AliakseiHryhoryeu/graduate-work-construction-engineer/Приложения/Приложение А.rtf

1. Плита: Плита87 - Плита № 87

1.1. Армирование:

• Тип : Плиты
• Направление рабочей арматуры : 0°
Основной класс арматуры : Нормативная прочность = 500,00 МПа
Горизонтальная ветвь графика зависимости напряжений от деформации
• Класс пластичности : C
• Диаметры стержней нижняя d1 = 1,6 (см) d2 = 1,6 (см)
верх d1 = 1,6 (см) d2 = 1,6 (см)
• Защитный слой нижняя c1 = 3,0 (см)
верх c2 = 3,0 (см)
• Отклонения защитного слоя Cdev = 1,0(см), Cdur = 0,0(см)

1.2. Бетон

Класс : C25/30; Нормативная прочность = 25,00 МПа
Прямоугольное распределение напряжений [3.1.7(3)]
• Плотность : 2501,36 (кГ/м3)
• Коэффициент ползучести бетона : 1,53
• Марка цемента : N

1.3. Гипотеза

• Расчеты по : EN 1992-1-1:2004/A1:2014
• Методы расчета площади арматуры : аналитический
• Допустимая ширина раскрытия трещин
- верхний слой : 0,40 (мм)
- нижний слой : 0,40 (мм)
• Допустимый прогиб : 3,0 (см)
• Проверка продавливания : да
• Внешние воздействия
- верхний слой : X0
- нижний слой : X0
• Тип расчета : чистый изгиб
• Класс конструкции : S1

1.4. Геометрия пластины

Толщина 0,30 (м)

Контур:
ребро начало конец длина
x1 y1 x2 y2 (м)
1 13,60 -27,25 13,60 -7,20 20,05
2 13,60 -7,20 13,71 -7,20 0,11
3 13,71 -7,20 14,33 -7,20 0,62
4 14,33 -7,20 14,91 -6,62 0,82
5 14,91 -6,62 14,91 -0,58 6,04
6 14,91 -0,58 14,33 0,00 0,82
7 14,33 0,00 13,71 0,00 0,62
8 13,71 0,00 0,00 0,00 13,71
9 0,00 0,00 0,00 -18,00 18,00
10 0,00 -18,00 -1,80 -18,00 1,80
11 -1,80 -18,00 -1,80 -43,20 25,20
12 -1,80 -43,20 -0,00 -43,20 1,80
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
22 11,97 8
28 0,54 40
28 0,74 38
28 3,13 4
28 3,33 20
28 6,04 2
28 6,34 2
28 6,64 2
28 6,83 32
28 6,94 2
28 7,14 10
28 7,36 16
28 8,40 18
28 8,46 16
28 8,92 24
28 8,93 9
28 9,00 8
28 9,44 8
28 9,45 12
28 9,60 18
28 9,97 12
28 10,13 11
28 10,66 4
28 10,73 94
28 11,26 188
28 11,36 20
28 11,90 30
