AliakseiHryhoryeu/graduate-work-construction-engineer/2. Расчетно-конструктивный раздел/Мое/Расчетный раздел.docx

2 Расчетно – конструктивный раздел

2.1 Расчет и конструирование перекрытия кровли в монолитном

железобетоне

Дипломный проект выполнен в монолитном железобетонном исполнении и включает в себя расчет и конструирование программным методом монолитного перекрытия. Расчет выполняется с применением программ Autodesk Robot Structural Analysis Professional 2021 путем интеграции 3D модели проекта из Autodesk Revit 2021. Результаты расчета и армирования экспортируются в изначальную модель для формирования необходимых чертежей.

Таблица 2.1 – Исходные данные

Тип здания | Гражданское
Размер здания в плане А х Б | 14,2х60,0 м
Количество этажей n1 | 10
Высота этажа Н1 | 3 м
Район строительства | г.Минск
Снеговая нагрузка S0 | 1,87 кПа

Таблица 2.2 – Характеристики материалов монолитного варианта

Конструкция | Класс бетона | Класс рабочей арматуры
Плита | С25/30 | S500

2.2 Подсчет нагрузок на плиту

Таблица 2.3 Нагрузки на плиту покрытия

Вид нагрузки | Нормативная нагрузка, кПа | | Расчетная нагруз- ка, кПа
Постоянная g:
ж/б плита (t=0,3м, ρ=25кН/м³) | 7,5 | 1,35 | 10,125
0,3∙25=7,5 кПа
Пароизоляционная пленка „Технониколь” (t=0,003 м, ρ=12 кН/м3) | 0,036 | 1,35 | 0,0486
0,003∙12=0,036 кПа
Керамзит(t=0,1 м, ρ=2 кН/м3) | 0,2 | 1,35 | 0.27
0,1∙2=0,2 кПа
Теплоизоляция из пенополистирола (t=0,3м, ρ=1,25 кН/м³) | 0,125 | 1,35 | 0,167
0,25∙0,5=0,125 кПа
Цементно-песчаная стряжка М100(t=0,03 м, ρ=24 кН/м³) | 0,72 | 1,35 | 0,972
0,03∙24=0,72 кПа
Два слоя битумно-полимерного материала ”Кровляэласт” К-СТ-БЭ-М/ПП-3,5 СТБ 1107-98 (t=0,003 м, ρ=12,0 кН/м³) | 0,036 | 1,35 | 0,049
0,003∙12=0,36 кПа
Итого постоянная: | gk=8.617 | | gd=11.632
Переменная q: снег | 1,872 | 1,5 | 2,823

Расчет программным комплексом Autodesk Robot Structural Analysis 2021 представлен в приложении А.

Изм. Кол. Лист №док. Подпись Дата Лист 923/21 - ПЗ
