AliakseiHryhoryeu/graduate-work-construction-engineer/5. Экономика/Курсовой/Приложение Г.rtf

www.BelStroyka.by верс. 1.17.13 | Приложение Г
Подрядчик: Наименование подрядчика
Наименование объекта:
Код объекта:
В е д о м о с т ь о б ъ е м о в р а б о т и р а с х о д а р е с у р с о в
Обоснование | Наименование видов работ | Объем | Наименование ресурсов | Единица измерения | Количество
| | Единица измерения
1 | 2 | 3 | 4 | 5 | 6
| Подземная часть | | Трудозатраты рабочих | чел.-час. | 79.36
| | | Трудозатраты рабочих, обслуживающих машины и механизмы | чел.-час. | 106.17
| | | Механизмы
М060247 | | | Экскаваторы одноковшовые дизельные на гусеничном ходу 0,5 м3 | МАШ.-Ч | 77.9218
М070149 | | | Бульдозеры 79 (108) квт (л.с.) | МАШ.-Ч | 28.2525
| | | Материалы
С412-1290-3 | | | Щебень из гравия марки 800, 2 класса, фракции 20-80 мм | М3 | 0.0729
| Фундаменты | | Трудозатраты рабочих | чел.-час. | 20621.34
| | | Трудозатраты рабочих, обслуживающих машины и механизмы | чел.-час. | 1330.54
| | | Механизмы
М020129 | | | Краны башенные 8 т | МАШ.-Ч | 206.9064
М020130 | | | Краны башенные 10 т | МАШ.-Ч | 173.9203
М021141 | | | Краны на автомобильном ходу 10 т | МАШ.-Ч | 49.5628
М030101 | | | Автопогрузчики 5 т | МАШ.-Ч | 81.57556
М040502 | | | Установки для сварки ручной дуговой (постоянного тока) | МАШ.-Ч | 183.0918
М050102 | | | Компрессоры передвижные с двигателем внутреннего сгорания давлением до 686 кпа (7атм) 5 м3/мин | МАШ.-Ч | 64.554
М070149 | | | Бульдозеры 79 (108) квт (л.с.) | МАШ.-Ч | 2.955
М110101 | | | Бадьи емкостью 2 м3 | МАШ.-Ч | 70.525
М110102 | | | Бадьи емкостью 4 м3 | МАШ.-Ч | 77.6677
М110610 | | | Смеситель-перегружатель 3 м3 | МАШ.-Ч | 2.1762
М110907 | | | Вибраторы | МАШ.-Ч | 77.6677
М111100 | | | Вибратор глубинный | МАШ.-Ч | 46.025
М121003 | | | Котлы битумные передвижные 400 л | МАШ.-Ч | 14.8707
М140110 | | | Агрегаты копровые без дизель-молота на базе трактора 80 (108) квт (л.с.) | МАШ.-Ч | 561.792
М140504 | | | Дизель-молоты 2,5 т | МАШ.-Ч | 561.792
М150702 | | | Краны-трубоукладчики для труб диаметром до 700 мм, грузоподъемностью 12,5 т | МАШ.-Ч | 155.648
М330302 | | | Машины шлифовальные угловые | МАШ.-Ч | 3.15
М331101 | | | Трамбовки пневматические (без учета стоимости сжатого воздуха) | МАШ.-Ч | 64.554
М331617 | | | Средства малой механизации | МАШ.-Ч | 31.4523
| | | Материалы
С101-129900 | | | Топливо дизельное из малосернистых нефтей | Т | 0.218426
С101-151300 | | | Электроды типа э42 диаметром 4 мм | Т | 0.000245

Обоснование | Наименование видов работ | Объем | Наименование ресурсов | Единица измерения | Количество
| | Единица измерения
1 | 2 | 3 | 4 | 5 | 6
С101-152900 | | | Электроды типа э42 диаметром 6 мм | Т | 0.2254
С101-17500-1 | | | Гвозди строительные | КГ | 108.328
С101-47101 | | | Краска масляная ма-15, сурик железный | Т | 0.0031616
С101-48604 | | | Круг отрезной 125х1,6х22 для резки металла | ШТ | 0.7875
С101-61200 | | | Мастика битумно-масляная морозостойкая мб-50 | Т | 1.6926
С101-81600 | | | Проволока стальная низкоуглеродистая общего назначения термически обработанная, без покрытия (светлая и черная), диаметром 1,1 мм | Т | 0.07
С101-85801 | | | Рубероид подкладочный с пылевидной посыпкой рпп-300 | М2 | 886.6
С101-87400 | | | Сетка проволочная тканая с квадратными ячейками n 05 без покрытия | М2 | 9.24
С101-96200 | | | Смазка солидол жировой (солидол-ж) | Т | 0.15543
С102-16000 | | | Доски обрезные из мягколиственных пород и березы длиной 4-6,5 м, толщиной 45 мм и более, 2 сорта | М3 | 1.4592
С102-2500 | | | Бруски обрезные хвойных пород длиной 4-6,5 м, шириной 75-150 мм, толщиной 40-75 мм, 3 сорта | М3 | 5.206
С102-3200 | | | Брусья обрезные хвойных пород длиной 4-6,5 м, шириной 150мм, толщиной 150 мм и более, 2 сорта | М3 | 0.822
С102-5300 | | | Доски обрезные хвойных пород длиной 4-6,5 м, шириной 75-150 мм, толщиной 25 мм, 3 сорта | М3 | 0.4384
С102-6100 | | | Доски обрезные хвойных пород длиной 4-6,5 м, шириной 75-150 мм, толщиной 44 мм и более, 3 сорта | М3 | 2.3288
С102-8000 | | | Доски необрезные хвойных пород длиной 4-6,5 м, толщиной 44 мм и более, 2 сорта | М3 | 0.2478
С113-12904-12 | | | Пленка полиэтиленовая первого сорта, толщиной 0,2 мм | М2 | 180.0575
С203-49801 | | | Щиты из досок толщина 25 мм | М2 | 92.082
С203-49802 | | | Щиты из досок толщина 40 мм | М2 | 12.312
С204-2900 | | | Заготовки из проволоки из низкоуглеродистой стали холоднотянутой периодического профиля класса вр-i для армирования железобетонных конструкций диаметром 4 мм | Т | 11.086912
С204-6200 | | | Детали закладные, изготовленные без применения сварки, гнутья, сверления (пробивки) отверстий, поставляемые отдельно | Т | 0.07
С204-6400 | | | Детали закладные, изготовленные с применением сварки, гнутья, сверления (пробивки) отверстий (при наличии одной из этих операций или всего перечня в любых сочетаниях), поставляемые отдельно | Т | 2.432
С412-9005 | | | Вода | М3 | 2.394
С414-1003 | | | Бетон тяжелый с крупностью заполнителя 20-40 мм, класса в7,5 | М3 | 347.13
С414-1005 | | | Бетон тяжелый с крупностью заполнителя 20-40 мм, класса с12/15 (b15) | М3 | 14.21
С414-1005-3 | | | Бетон тяжелый с крупностью заполнителя более 10 до 20 мм, класса с12/15 (b15) | М3 | 139.055
С414-1009 | | | Бетон тяжелый с крупностью заполнителя 20-40 мм, класса с25/30 (в30) | М3 | 177.625
С414-2001 | | | Растворы кладочные тяжелые цементные, марки 25 | М3 | 10.075
С101-115100 | | | Сталь арматурная горячекатаная гладкая для железобетонных конструкций, класса s240 (а240), диаметром 12 мм | Т | 431.055
С101-118715 | | | Сталь арматурная горячекатаная периодического профиля для железобетонных конструкций, класса s500, диаметром 20 мм | Т | 143.685
| Несущие конструкции | | Трудозатраты рабочих | чел.-час. | 67520.41
| | | Трудозатраты рабочих, обслуживающих машины и механизмы | чел.-час. | 1486.24
| | | Механизмы
М020129 | | | Краны башенные 8 т | МАШ.-Ч | 661.5864
М020130 | | | Краны башенные 10 т | МАШ.-Ч | 331.356
М021141 | | | Краны на автомобильном ходу 10 т | МАШ.-Ч | 53.0276
М030101 | | | Автопогрузчики 5 т | МАШ.-Ч | 268.2288

Обоснование | Наименование видов работ | Объем | Наименование ресурсов | Единица измерения | Количество
| | Единица измерения
1 | 2 | 3 | 4 | 5 | 6
М040502 | | | Установки для сварки ручной дуговой (постоянного тока) | МАШ.-Ч | 1894.9606
М110101 | | | Бадьи емкостью 2 м3 | МАШ.-Ч | 47.304
М110102 | | | Бадьи емкостью 4 м3 | МАШ.-Ч | 601.509
М110907 | | | Вибраторы | МАШ.-Ч | 601.509
М111100 | | | Вибратор глубинный | МАШ.-Ч | 41.2308
М330302 | | | Машины шлифовальные угловые | МАШ.-Ч | 0.7848
М331617 | | | Средства малой механизации | МАШ.-Ч | 172.0374
| | | Материалы
С101-151300 | | | Электроды типа э42 диаметром 4 мм | Т | 0.0003204
С101-152900 | | | Электроды типа э42 диаметром 6 мм | Т | 2.3308
С101-17500-1 | | | Гвозди строительные | КГ | 1095.324
С101-48604 | | | Круг отрезной 125х1,6х22 для резки металла | ШТ | 0.198
С101-81600 | | | Проволока стальная низкоуглеродистая общего назначения термически обработанная, без покрытия (светлая и черная), диаметром 1,1 мм | Т | 0.0195192
С101-96200 | | | Смазка солидол жировой (солидол-ж) | Т | 1.4521
С102-2500 | | | Бруски обрезные хвойных пород длиной 4-6,5 м, шириной 75-150 мм, толщиной 40-75 мм, 3 сорта | М3 | 52.06
С102-3200 | | | Брусья обрезные хвойных пород длиной 4-6,5 м, шириной 150мм, толщиной 150 мм и более, 2 сорта | М3 | 8.22
С102-5300 | | | Доски обрезные хвойных пород длиной 4-6,5 м, шириной 75-150 мм, толщиной 25 мм, 3 сорта | М3 | 4.384
С102-6100 | | | Доски обрезные хвойных пород длиной 4-6,5 м, шириной 75-150 мм, толщиной 44 мм и более, 3 сорта | М3 | 21.92
С102-8000 | | | Доски необрезные хвойных пород длиной 4-6,5 м, толщиной 44 мм и более, 2 сорта | М3 | 3.0444
С113-12904-12 | | | Пленка полиэтиленовая первого сорта, толщиной 0,2 мм | М2 | 329.452
С203-49801 | | | Щиты из досок толщина 25 мм | М2 | 966.58
С204-2900 | | | Заготовки из проволоки из низкоуглеродистой стали холоднотянутой периодического профиля класса вр-i для армирования железобетонных конструкций диаметром 4 мм | Т | 35.806708
С204-6200 | | | Детали закладные, изготовленные без применения сварки, гнутья, сверления (пробивки) отверстий, поставляемые отдельно | Т | 0.0915624
С414-1005 | | | Бетон тяжелый с крупностью заполнителя 20-40 мм, класса с12/15 (b15) | М3 | 174.58
С414-1005-3 | | | Бетон тяжелый с крупностью заполнителя более 10 до 20 мм, класса с12/15 (b15) | М3 | 1390.55
С414-1009 | | | Бетон тяжелый с крупностью заполнителя 20-40 мм, класса с25/30 (в30) | М3 | 36.54
С101-115100 | | | Сталь арматурная горячекатаная гладкая для железобетонных конструкций, класса s240 (а240), диаметром 12 мм | Т | 1378.306
С101-118715 | | | Сталь арматурная горячекатаная периодического профиля для железобетонных конструкций, класса s500, диаметром 20 мм | Т | 459.435
| Наружная отделка фасадов | | Трудозатраты рабочих | чел.-час. | 17953.75
| | | Трудозатраты рабочих, обслуживающих машины и механизмы | чел.-час. | 1437.94
| | | Механизмы
М020130 | | | Краны башенные 10 т | МАШ.-Ч | 159.7008
М021141 | | | Краны на автомобильном ходу 10 т | МАШ.-Ч | 11.8768
М050102 | | | Компрессоры передвижные с двигателем внутреннего сгорания давлением до 686 кпа (7атм) 5 м3/мин | МАШ.-Ч | 898.3854
М330302 | | | Машины шлифовальные угловые | МАШ.-Ч | 91.8136
М331400 | | | Станок камнерезный универсальный | МАШ.-Ч | 88.8777
М331451 | | | Перфораторы электрические | МАШ.-Ч | 561.0238

Обоснование | Наименование видов работ | Объем | Наименование ресурсов | Единица измерения | Количество
| | Единица измерения
1 | 2 | 3 | 4 | 5 | 6
М331604 | | | Станок передвижной для сверления отверстий в железобетоне диаметром 20-160 мм | МАШ.-Ч | 890.3784
М331615 | | | Дрели электрические | МАШ.-Ч | 1148.4175
М331617 | | | Средства малой механизации | МАШ.-Ч | 279.1048
М351302 | | | Электрофен | МАШ.-Ч | 222.5946
| | | Материалы
С101-10110-1 | | | Болты строительные с гайками и шайбами диаметром 8-12мм | Т | 0.341632
С101-115000 | | | Сталь арматурная горячекатаная гладкая для железобетонных конструкций, класса s240 (а240), диаметром 10 мм | Т | 0.99813
С101-11602-15 | | | Винты самонарезающие с полукруглой головкой диаметром 6-10мм длиной 50мм | КГ | 62.3532
С101-11602-6 | | | Винты с полукруглой головкой 4х30 мм гост 17473-80 | КГ | 6.4056
С101-11602-7 | | | Винты с полукруглой головкой 5х20 мм гост 17473-80 | КГ | 21.0851
С101-11602-9 | | | Винты самонарезающие с полуцилиндрической головкой для металла | КГ | 46.1737
С101-123402 | | | Сталь тонколистовая оцинкованная углеродистая толщиной 0,8 мм | КГ | 3003.2976
С101-123403 | | | Сталь тонколистовая оцинкованная углеродистая толщиной 0,5 мм | Т | 0.4810104
С101-138010 | | | Растворная смесь сухая, кладочная, цементная, для кирпича, камней, блоков, с водоудерживающей добавкой, м100/м150, f75 | Т | 20.262039
С101-149003-1 | | | Шайба плоская оцинкованная | ШТ | 13184.86
С101-149004 | | | Прокладки паронитовые | КГ | 111.0304
С101-18001 | | | Гвозди строительные оцинкованные | Т | 2.794764
С101-24301 | | | Заклепки комбинированные для соединения профилированного стального настила и разнообразных листов | Т | 0.0568497
С101-48602 | | | Круг отрезной 230х2х22 для резки камня, бетона | ШТ | 66.725
С101-48604 | | | Круг отрезной 125х1,6х22 для резки металла | ШТ | 66.4581
С101-79201-3 | | | Прокладки изолирующие пластмассовые | ШТ | 8327.28
С101-81100 | | | Проволока стальная низкоуглеродистая общего назначения термически обработанная, оцинкованная, диаметром 1,1 мм | Т | 0.2612896
С101-81201-1 | | | Проволока стальная низкоуглеродистая общего назначения термически обработанная, оцинкованная, диаметром 5 мм | Т | 0.3236428
С101-81404-1 | | | Проволока стальная низкоуглеродистая общего назначения термически обработанная, оцинкованная, диаметром 2 мм | КГ | 41.5688
С101-82905 | | | Пряжка бандажная тип 1-о | КГ | 8.9076
С101-85801 | | | Рубероид подкладочный с пылевидной посыпкой рпп-300 | М2 | 598.878
С101-86720 | | | Сверла спиральные с цилиндрическим хвостовиком, длинная серия (по металлу), диаметром 3,1-3,7мм | ШТ | 142.7915
С101-86721 | | | Сверла спиральные с цилиндрическим хвостовиком, длинная серия (по металлу), диаметром 4,3-5,3мм | ШТ | 150.5316
С101-86723 | | | Сверла спиральные с цилиндрическим хвостовиком, длинная серия (по металлу), диаметром 9,6-10,6 мм | ШТ | 29.6259
С101-86726-38 | | | Сверла по бетону с sds хвостовиком (наконечник из твердосплавной стали), диаметром 10-12 мм, длиной 110-165 мм | ШТ | 111.0304
С104-427 | | | Плиты теплоизоляционные из минерального стекловолокна isover kl 37, толщиной 50 мм | М3 | 9.1332592
С104-713 | | | Плиты теплоизоляционные пенополистирольные ппт-15а (ппт-15н-а) | М3 | 203.61852
С204-6400 | | | Детали закладные, изготовленные с применением сварки, гнутья, сверления (пробивки) отверстий (при наличии одной из этих операций или всего перечня в любых сочетаниях), поставляемые отдельно | Т | 0.0576504
С412-9005 | | | Вода | М3 | 6.103623

Обоснование | Наименование видов работ | Объем | Наименование ресурсов | Единица измерения | Количество
| | Единица измерения
1 | 2 | 3 | 4 | 5 | 6
С414-3036-36 | | | Блоки из ячеистых бетонов стеновые мелкие, 1 категории, класс бетона в2, плотность 600 кг/м3 | М3 | 818.4666
| Стены и перегородки | | Трудозатраты рабочих | чел.-час. | 5559.43
| | | Трудозатраты рабочих, обслуживающих машины и механизмы | чел.-час. | 311.41
| | | Механизмы
М020130 | | | Краны башенные 10 т | МАШ.-Ч | 275.9932
М030101 | | | Автопогрузчики 5 т | МАШ.-Ч | 1.0875
М040502 | | | Установки для сварки ручной дуговой (постоянного тока) | МАШ.-Ч | 148.8909
М110101 | | | Бадьи емкостью 2 м3 | МАШ.-Ч | 115.9776
М110102 | | | Бадьи емкостью 4 м3 | МАШ.-Ч | 58.455
М110610 | | | Смеситель-перегружатель 3 м3 | МАШ.-Ч | 12.3332
М110907 | | | Вибраторы | МАШ.-Ч | 58.455
М111100 | | | Вибратор глубинный | МАШ.-Ч | 103.7304
М330302 | | | Машины шлифовальные угловые | МАШ.-Ч | 0.3744
М331617 | | | Средства малой механизации | МАШ.-Ч | 21.9959
| | | Материалы
С101-151300 | | | Электроды типа э42 диаметром 4 мм | Т | 0.002448
С101-152900 | | | Электроды типа э42 диаметром 6 мм | Т | 0.1725
С101-17500-1 | | | Гвозди строительные | КГ | 47.625
С101-48604 | | | Круг отрезной 125х1,6х22 для резки металла | ШТ | 0.0936
С101-81600 | | | Проволока стальная низкоуглеродистая общего назначения термически обработанная, без покрытия (светлая и черная), диаметром 1,1 мм | Т | 0.0113184
С101-96200 | | | Смазка солидол жировой (солидол-ж) | Т | 0.20625
С102-2500 | | | Бруски обрезные хвойных пород длиной 4-6,5 м, шириной 75-150 мм, толщиной 40-75 мм, 3 сорта | М3 | 6.45
С102-3200 | | | Брусья обрезные хвойных пород длиной 4-6,5 м, шириной 150мм, толщиной 150 мм и более, 2 сорта | М3 | 1.05
С102-6100 | | | Доски обрезные хвойных пород длиной 4-6,5 м, шириной 75-150 мм, толщиной 44 мм и более, 3 сорта | М3 | 1.8825
С113-12904-12 | | | Пленка полиэтиленовая первого сорта, толщиной 0,2 мм | М2 | 11.3184
С203-39600-1 | | | Пробки деревянные | М3 | 2.295657
С203-49801 | | | Щиты из досок толщина 25 мм | М2 | 137.25
С204-6200 | | | Детали закладные, изготовленные без применения сварки, гнутья, сверления (пробивки) отверстий, поставляемые отдельно | Т | 0.2614608
С412-9005 | | | Вода | М3 | 162.574
С413-2040-2 | | | Кирпич силикатный утолщенный, полнотелый, обыкновенный, рядовой размером 250х120х88 мм, марки 125 | 1000 ШТ | 107.9155
С414-1005-3 | | | Бетон тяжелый с крупностью заполнителя более 10 до 20 мм, класса с12/15 (b15) | М3 | 76.125
С414-1009 | | | Бетон тяжелый с крупностью заполнителя 20-40 мм, класса с25/30 (в30) | М3 | 73.08
С414-2008 | | | Растворы кладочные цементно-известковые, марки 50 | М3 | 58.0221
| Кровля | | Трудозатраты рабочих | чел.-час. | 2094.71
| | | Трудозатраты рабочих, обслуживающих машины и механизмы | чел.-час. | 71.73
| | | Механизмы
М020130 | | | Краны башенные 10 т | МАШ.-Ч | 8.8865
М021141 | | | Краны на автомобильном ходу 10 т | МАШ.-Ч | 0.0304
М031110 | | | Подъемники строительные 0,5 т | МАШ.-Ч | 16.416
М031801 | | | Вышки телескопические 0,35 т | МАШ.-Ч | 19.2375
М040502 | | | Установки для сварки ручной дуговой (постоянного тока) | МАШ.-Ч | 7.16

Обоснование | Наименование видов работ | Объем | Наименование ресурсов | Единица измерения | Количество
| | Единица измерения
1 | 2 | 3 | 4 | 5 | 6
М050401 | | | Компрессоры передвижные с электродвигателем давлением 600 кпа (6 атм) 0,5 м3/мин | МАШ.-Ч | 2.394
М111301 | | | Вибратор поверхностный | МАШ.-Ч | 102.6
М121003 | | | Котлы битумные передвижные 400 л | МАШ.-Ч | 33.6015
М134041 | | | Шуруповерт | МАШ.-Ч | 34.96
М150402 | | | Газовая горелка | МАШ.-Ч | 30.79
М331451 | | | Перфораторы электрические | МАШ.-Ч | 6.3308
М331615 | | | Дрели электрические | МАШ.-Ч | 89.68
М331617 | | | Средства малой механизации | МАШ.-Ч | 27.1579
| | | Материалы
С101-123403 | | | Сталь тонколистовая оцинкованная углеродистая толщиной 0,5 мм | Т | 4.959
С101-129900 | | | Топливо дизельное из малосернистых нефтей | Т | 0.48735
С101-135500 | | | Цемент гипсоглиноземистый расширяющийся | Т | 0.00064
С101-149001 | | | Шурупы-саморезы 4,8х28 мм | ШТ | 608
С101-149002 | | | Шурупы-саморезы 4,8х19 мм | ШТ | 304
С101-151400-1 | | | Электроды типа э42а диаметром 4 мм | КГ | 0.76
С101-15500-10 | | | Дюбель металлический рамный 10х72 | 10 ШТ | 15.2
С101-15512 | | | Дюбель с шурупом для быстрого монтажа 8х80 мм | 100 ШТ | 41.04
С101-19000 | | | Гвозди тарные круглые 3х80 мм | Т | 0.09747
С101-32200 | | | Керосин технический экологически чистый | Т | 1.0089
С101-59400 | | | Мастика битумная кровельная горячая | Т | 3.8304
С101-63205-1 | | | Льняная прядь | КГ | 0.24
С101-7600 | | | Битумы нефтяные кровельные марки бнк-90/30 | Т | 0.21375
С101-7800 | | | Битумы нефтяные кровельные марки бнк-45/180 | Т | 0.21375
С101-82511 | | | Смесь пропана и бутана технических | КГ | 364.9964
С101-85801 | | | Рубероид подкладочный с пылевидной посыпкой рпп-300 | М2 | 171.855
С101-86721 | | | Сверла спиральные с цилиндрическим хвостовиком, длинная серия (по металлу), диаметром 4,3-5,3мм | ШТ | 5.928
С101-86726-20 | | | Сверла по бетону с sds хвостовиком (наконечник из твердосплавной стали), диаметром 8-10 мм, длиной 260 (265) мм | ШТ | 25.65
С101-86726-38 | | | Сверла по бетону с sds хвостовиком (наконечник из твердосплавной стали), диаметром 10-12 мм, длиной 110-165 мм | ШТ | 1.52
С102-12100 | | | Доски обрезные хвойных пород длиной 2-3,75 м, шириной 75-150 мм, толщиной 44 мм и более, 3 сорта | М3 | 38.0475
С113-12904-12 | | | Пленка полиэтиленовая первого сорта, толщиной 0,2 мм | М2 | 171
С117-1404 | | | Мастика битумная полимерная холодная (мбпх) для нанесения на рулонные материалы | Т | 0.49932
С204-6400-2 | | | Крючья металлические массой 0,5 кг | КГ | 56.43
С412-9005 | | | Вода | М3 | 10.26
С414-2004 | | | Растворы кладочные тяжелые цементные, марки 100 | М3 | 27.3201
| Окна | | Трудозатраты рабочих | чел.-час. | 2113.03
| | | Трудозатраты рабочих, обслуживающих машины и механизмы | чел.-час. | 0
| | | Механизмы
М331615 | | | Дрели электрические | МАШ.-Ч | 302.2368
| | | Материалы
С101-148000 | | | Шурупы с полукруглой головкой 3,5х35 мм | Т | 0.0093819
С101-148200 | | | Шурупы с полукруглой головкой 5х70 мм | Т | 0.0741131
С101-149010-5 | | | Шурупы универсальные 6х100 мм | 1000 ШТ | 0.225

Обоснование | Наименование видов работ | Объем | Наименование ресурсов | Единица измерения | Количество
| | Единица измерения
1 | 2 | 3 | 4 | 5 | 6
С101-15500-12 | | | Дюбель полипропиленовый 10х50, 10х80 | ШТ | 7975.8
С101-21603 | | | Герметик силиконовый 280мл | ШТ | 45.88
С101-51512-7 | | | Лента паропроницаемая саморасширяющаяся уплотнительная (псул) шириной 12 мм с максимальным расширением ленты 30 мм | М | 244.65
С101-51521-2 | | | Лента самоклеящаяся неотверждаемая гидро-пароизоляционная бутилкаучуковая, армированная нетканым полотном ("викар с" марки лт (о)) шириной 120-150 мм, толщиной 1,5 мм | М | 244.65
С101-79100-1 | | | Пена полиуретановая монтажная производственная в аэрозольной упаковке | МЛ | 26382.9
С414-2004 | | | Растворы кладочные тяжелые цементные, марки 100 | М3 | 0.33
С203-52120 | | | Окно из поливинилхлоридного профиля brugmann оп а 600-600 п/о сп2 т, с поворотно-откидным устройством, с двухкамерным стеклопакетом, теплозащитное | М2 | 9.65
С203-52139 | | | Окно из поливинилхлоридного профиля brugmann оп а 1500-1500 п/о и г сп2 т, с поворотно-откидным устройством, с импостом, с глухой створкой, с двухкамерным стеклопакетом, теплозащитное | М2 | 194.48
С203-52144 | | | Окно из поливинилхлоридного профиля brugmann оп а 1500-2100 п/у и г и п/о сп2 т, с поворотным устройством, с глухой створкой, с поворотно-откидным устройством, с двумя импостами, с двухкамерным стеклопакетом, теплозащитное | М2 | 496.08
| Двери | | Трудозатраты рабочих | чел.-час. | 200.62
| | | Трудозатраты рабочих, обслуживающих машины и механизмы | чел.-час. | 10.87
| | | Механизмы
М021143 | | | Краны на автомобильном ходу 16 т | МАШ.-Ч | 0.5964
М121003 | | | Котлы битумные передвижные 400 л | МАШ.-Ч | 0.1684
М331617 | | | Средства малой механизации | МАШ.-Ч | 10.267
| | | Материалы
С101-148000 | | | Шурупы с полукруглой головкой 3,5х35 мм | Т | 4E-5
С101-17500-1 | | | Гвозди строительные | КГ | 17.047
С101-21903 | | | Вяжущее гипсовое марки г-4 нормальнотвердеющее (б), среднего помола (ii) (фасованное) | Т | 0.00146
С101-85801 | | | Рубероид подкладочный с пылевидной посыпкой рпп-300 | М2 | 8.18
С102-24600 | | | Дрова разделанные длиной 1 м осина, ольха, нижний лесосклад | М3 | 0.00684
С102-5300 | | | Доски обрезные хвойных пород длиной 4-6,5 м, шириной 75-150 мм, толщиной 25 мм, 3 сорта | М3 | 0.1376
С414-2012 | | | Растворы отделочные тяжелые известковые, в соотношении 1 3 | М3 | 0.00964
С203-20063 | | | Блок дверной наружный деревянный двупольный, частично остекленный, с порогом, щитовой дн д ч 21-12 п щ | М2 | 6
С203-19859-2 | | | Блок дверной внутренний межкомнатный деревянный, двупольный, глухой, щитовой дв1 д г 21-12 щ | М2 | 166.2
| Внутренние отделочные работы | | Трудозатраты рабочих | чел.-час. | 19176.39
| | | Трудозатраты рабочих, обслуживающих машины и механизмы | чел.-час. | 15.28
| | | Механизмы
М030401 | | | Лебедки электрические тяговым усилием до 5,79 (0,59) кн (т) | МАШ.-Ч | 13.608
М030404 | | | Лебедки электрические тяговым усилием до 31,39 (3,2) кн (т) | МАШ.-Ч | 0.49004
М331615 | | | Дрели электрические | МАШ.-Ч | 67.8081
М331617 | | | Средства малой механизации | МАШ.-Ч | 15.2753
| | | Материалы
С101-11099 | | | Шкурка шлифовальная на бумажной основе водостойкая | М2 | 315.794
С101-11401 | | | Ветошь | КГ | 14.7001
С101-138005-2 | | | Шпатлевка клеемасляная | Т | 4.77789

Обоснование | Наименование видов работ | Объем | Наименование ресурсов | Единица измерения | Количество
| | Единица измерения
1 | 2 | 3 | 4 | 5 | 6
С101-21903 | | | Вяжущее гипсовое марки г-4 нормальнотвердеющее (б), среднего помола (ii) (фасованное) | Т | 0.09
С101-32905 | | | Клей кмц (для обоев) | Т | 0.1813148
С101-34066 | | | Краска акриловая для внутренних работ (сп "колор" ооо), белая | КГ | 3112.55
С101-62617 | | | Обои бумажные дуплекс с полутоновым рисунком | 100 М2 | 140.8865
С101-63100 | | | Опилки древесные | М3 | 2.50635
С113-3601 | | | Дисперсия поливинилацетатная непластифицированная марки д50н | КГ | 350.3786
С412-9005 | | | Вода | М3 | 18.69406
С414-2013 | | | Растворы отделочные тяжелые известковые, в соотношении 1 2,5 | М3 | 0.234
С414-9014 | | | Растворы отделочные тяжелые цементные, приготовленные в построечных условиях, состав 1 3 | М3 | 40.425
С414-9015 | | | Растворы отделочные тяжелые цементно-известковые, приготовленные в построечных условиях, состав 1 1 6 | М3 | 11.202
| Тип 1(пол подвала) | | Трудозатраты рабочих | чел.-час. | 58.94
| | | Трудозатраты рабочих, обслуживающих машины и механизмы | чел.-час. | 2.75
| | | Механизмы
М050101 | | | Компрессоры передвижные с двигателем внутреннего сгорания давлением до 686 кпа (7атм) 2,2 м3/мин | МАШ.-Ч | 1.131
М110907 | | | Вибраторы | МАШ.-Ч | 7.1775
М331617 | | | Средства малой механизации | МАШ.-Ч | 1.624
| | | Материалы
С101-128902 | | | Ткань мешочная | 10 М2 | 0.58
С412-9005 | | | Вода | М3 | 5.075
С414-1004-1 | | | Бетон тяжелый с крупностью заполнителя 10 мм и менее, класса с10/12,5 (в12,5) | М3 | 2.958
| Тип 2(пол 1го этажа коридоры) | | Трудозатраты рабочих | чел.-час. | 305.07
| | | Трудозатраты рабочих, обслуживающих машины и механизмы | чел.-час. | 18.48
| | | Механизмы
М020130 | | | Краны башенные 10 т | МАШ.-Ч | 5.9598
М050101 | | | Компрессоры передвижные с двигателем внутреннего сгорания давлением до 686 кпа (7атм) 2,2 м3/мин | МАШ.-Ч | 2.0124
М110907 | | | Вибраторы | МАШ.-Ч | 12.771
М331607 | | | Машина паркетно-шлифовальная | МАШ.-Ч | 20.0466
М331617 | | | Средства малой механизации | МАШ.-Ч | 10.5126
| | | Материалы
С101-11099 | | | Шкурка шлифовальная на бумажной основе водостойкая | М2 | 51.6
С101-128902 | | | Ткань мешочная | 10 М2 | 1.032
С101-18000 | | | Гвозди строительные с плоской головкой 1,8х50 мм | Т | 0.035604
С101-18100 | | | Гвозди строительные оцинкованные 1,8х60 мм | Т | 4.5E-5
С101-65200 | | | Плиты древесноволокнистые мокрого способа производства мягкие марки м-2 толщиной 12 мм | 1000 М2 | 0.26574
С412-9005 | | | Вода | М3 | 9.03
С414-1004-1 | | | Бетон тяжелый с крупностью заполнителя 10 мм и менее, класса с10/12,5 (в12,5) | М3 | 5.2632
| Тип 3(пол 1го этажа, сан. помещения) | | Трудозатраты рабочих | чел.-час. | 115.86
| | | Трудозатраты рабочих, обслуживающих машины и механизмы | чел.-час. | 3.01
| | | Механизмы
М020130 | | | Краны башенные 10 т | МАШ.-Ч | 0.88836
М050101 | | | Компрессоры передвижные с двигателем внутреннего сгорания давлением до 686 кпа (7атм) 2,2 м3/мин | МАШ.-Ч | 0.55224

Обоснование | Наименование видов работ | Объем | Наименование ресурсов | Единица измерения | Количество
| | Единица измерения
1 | 2 | 3 | 4 | 5 | 6
М110907 | | | Вибраторы | МАШ.-Ч | 5.27106
М331617 | | | Средства малой механизации | МАШ.-Ч | 1.57884
М121003 | | | Котлы битумные передвижные 400 л | МАШ.-Ч | 1.63194
М331305 | | | Пылесос промышленный | МАШ.-Ч | 1.0089
М331615 | | | Дрели электрические | МАШ.-Ч | 0.58356
М331618 | | | Электротермос | МАШ.-Ч | 0.64782
| | | Материалы
С101-128902 | | | Ткань мешочная | 10 М2 | 0.2832
С412-9005 | | | Вода | М3 | 2.478
С414-1004-1 | | | Бетон тяжелый с крупностью заполнителя 10 мм и менее, класса с10/12,5 (в12,5) | М3 | 0.72216
С101-1002 | | | Асбест хризотиловый марки а-6к-30 | Т | 0.002832
С101-11401 | | | Ветошь | КГ | 0.378
С101-28701 | | | Плитки керамические для полов основные неглазурованные (керамогранит) размером 300х300 мм, 303х303 мм | М2 | 36.462
С101-7000 | | | Бензин автомобильный аи-95 | Т | 0.020178
С101-7300 | | | Битумы нефтяные строительные марки бн-90/10 | Т | 0.055578
С101-7400 | | | Битумы нефтяные строительные марки бн-70/30 | Т | 0.006726
С113-10100 | | | Мука андезитовая кислотоупорная марки а | Т | 0.04425
С414-1013-1 | | | Бетон легкий (аглопорито- и керамзитобетон) с крупностью заполнителя 10 мм и менее, класса в12,5 | М3 | 0.72216
| Тип 4(пол 1го этажа в комнатах) | | Трудозатраты рабочих | чел.-час. | 1089.62
| | | Трудозатраты рабочих, обслуживающих машины и механизмы | чел.-час. | 51.96
| | | Механизмы
М020130 | | | Краны башенные 10 т | МАШ.-Ч | 20.6976
М050101 | | | Компрессоры передвижные с двигателем внутреннего сгорания давлением до 686 кпа (7атм) 2,2 м3/мин | МАШ.-Ч | 6.9888
М110907 | | | Вибраторы | МАШ.-Ч | 44.352
М331617 | | | Средства малой механизации | МАШ.-Ч | 24.2816
| | | Материалы
С101-128902 | | | Ткань мешочная | 10 М2 | 3.584
С412-9005 | | | Вода | М3 | 31.36
С414-1004-1 | | | Бетон тяжелый с крупностью заполнителя 10 мм и менее, класса с10/12,5 (в12,5) | М3 | 18.2784
С101-32903 | | | Клей бустилат | Т | 0.448
С101-55700 | | | Линолеум поливинилхлоридный на тканевой подоснове, звукоизолирующий декоративный "деколин" | М2 | 946.176
| Тип 5(пол типового этажа коридоры) | | Трудозатраты рабочих | чел.-час. | 1742.56
| | | Трудозатраты рабочих, обслуживающих машины и механизмы | чел.-час. | 81.91
| | | Механизмы
М050101 | | | Компрессоры передвижные с двигателем внутреннего сгорания давлением до 686 кпа (7атм) 2,2 м3/мин | МАШ.-Ч | 16.1148
М110907 | | | Вибраторы | МАШ.-Ч | 102.267
М331607 | | | Машина паркетно-шлифовальная | МАШ.-Ч | 160.5282
М331617 | | | Средства малой механизации | МАШ.-Ч | 65.7948
| | | Материалы
С101-11099 | | | Шкурка шлифовальная на бумажной основе водостойкая | М2 | 413.2
С101-128902 | | | Ткань мешочная | 10 М2 | 8.264
С101-18000 | | | Гвозди строительные с плоской головкой 1,8х50 мм | Т | 0.285108
С101-18100 | | | Гвозди строительные оцинкованные 1,8х60 мм | Т | 0.00036

Обоснование | Наименование видов работ | Объем | Наименование ресурсов | Единица измерения | Количество
| | Единица измерения
1 | 2 | 3 | 4 | 5 | 6
С101-65200 | | | Плиты древесноволокнистые мокрого способа производства мягкие марки м-2 толщиной 12 мм | 1000 М2 | 2.12798
С412-9005 | | | Вода | М3 | 72.31
С414-1004-1 | | | Бетон тяжелый с крупностью заполнителя 10 мм и менее, класса с10/12,5 (в12,5) | М3 | 42.1464
| Тип 6(пол типового этажа, сан помещения) | | Трудозатраты рабочих | чел.-час. | 1539.68
| | | Трудозатраты рабочих, обслуживающих машины и механизмы | чел.-час. | 26.49
| | | Механизмы
М050101 | | | Компрессоры передвижные с двигателем внутреннего сгорания давлением до 686 кпа (7атм) 2,2 м3/мин | МАШ.-Ч | 7.7376
М110907 | | | Вибраторы | МАШ.-Ч | 73.8544
М331617 | | | Средства малой механизации | МАШ.-Ч | 17.7072
М020130 | | | Краны башенные 10 т | МАШ.-Ч | 1.0544
М121003 | | | Котлы битумные передвижные 400 л | МАШ.-Ч | 22.8656
М331305 | | | Пылесос промышленный | МАШ.-Ч | 14.136
М331615 | | | Дрели электрические | МАШ.-Ч | 8.9184
М331618 | | | Электротермос | МАШ.-Ч | 9.0768
| | | Материалы
С101-128902 | | | Ткань мешочная | 10 М2 | 3.968
С412-9005 | | | Вода | М3 | 34.72
С414-1004-1 | | | Бетон тяжелый с крупностью заполнителя 10 мм и менее, класса с10/12,5 (в12,5) | М3 | 10.1184
С101-1002 | | | Асбест хризотиловый марки а-6к-30 | Т | 0.03968
С101-11401 | | | Ветошь | КГ | 5.76
С101-28701 | | | Плитки керамические для полов основные неглазурованные (керамогранит) размером 300х300 мм, 303х303 мм | М2 | 510.88
С101-7000 | | | Бензин автомобильный аи-95 | Т | 0.28272
С101-7300 | | | Битумы нефтяные строительные марки бн-90/10 | Т | 0.77872
С101-7400 | | | Битумы нефтяные строительные марки бн-70/30 | Т | 0.09424
С113-10100 | | | Мука андезитовая кислотоупорная марки а | Т | 0.62
С414-1013-1 | | | Бетон легкий (аглопорито- и керамзитобетон) с крупностью заполнителя 10 мм и менее, класса в12,5 | М3 | 10.1184
| Тип 7(пол типового этажа в помещениях) | | Трудозатраты рабочих | чел.-час. | 6287.05
| | | Трудозатраты рабочих, обслуживающих машины и механизмы | чел.-час. | 186.37
| | | Механизмы
М050101 | | | Компрессоры передвижные с двигателем внутреннего сгорания давлением до 686 кпа (7атм) 2,2 м3/мин | МАШ.-Ч | 55.9104
М110907 | | | Вибраторы | МАШ.-Ч | 354.816
М331617 | | | Средства малой механизации | МАШ.-Ч | 130.4576
| | | Материалы
С101-128902 | | | Ткань мешочная | 10 М2 | 28.672
С412-9005 | | | Вода | М3 | 250.88
С414-1004-1 | | | Бетон тяжелый с крупностью заполнителя 10 мм и менее, класса с10/12,5 (в12,5) | М3 | 146.2272
С101-32903 | | | Клей бустилат | Т | 3.584
С101-55700 | | | Линолеум поливинилхлоридный на тканевой подоснове, звукоизолирующий декоративный "деколин" | М2 | 7569.408
| Отмостка и крыльца | | Трудозатраты рабочих | чел.-час. | 455.98
| | | Трудозатраты рабочих, обслуживающих машины и механизмы | чел.-час. | 25.03
| | | Механизмы
М020130 | | | Краны башенные 10 т | МАШ.-Ч | 0.2337

Обоснование | Наименование видов работ | Объем | Наименование ресурсов | Единица измерения | Количество
| | Единица измерения
1 | 2 | 3 | 4 | 5 | 6
М021141 | | | Краны на автомобильном ходу 10 т | МАШ.-Ч | 6.633
М050102 | | | Компрессоры передвижные с двигателем внутреннего сгорания давлением до 686 кпа (7атм) 5 м3/мин | МАШ.-Ч | 16.7264
М110610 | | | Смеситель-перегружатель 3 м3 | МАШ.-Ч | 0.15746
М120906 | | | Катки дорожные самоходные гладкие 8 т | МАШ.-Ч | 0.24
М121003 | | | Котлы битумные передвижные 400 л | МАШ.-Ч | 1.8624
М331101 | | | Трамбовки пневматические (без учета стоимости сжатого воздуха) | МАШ.-Ч | 16.7264
М331617 | | | Средства малой механизации | МАШ.-Ч | 1.03654
| | | Материалы
С101-128902 | | | Ткань мешочная | 10 М2 | 3.18384
С101-129900 | | | Топливо дизельное из малосернистых нефтей | Т | 0.0293
С101-32200 | | | Керосин технический экологически чистый | Т | 0.03094
С101-59400 | | | Мастика битумная кровельная горячая | Т | 0.22707
С101-7600 | | | Битумы нефтяные кровельные марки бнк-90/30 | Т | 0.00958
С101-7800 | | | Битумы нефтяные кровельные марки бнк-45/180 | Т | 0.00352
С102-17200 | | | Бруски обрезные из мягколиственных пород и березы длиной 2-3,75 м, толщиной 32-70 мм, 2 сорта | М3 | 0.0806
С412-1283 | | | Щебень из природного камня для строительных работ марки 400, фракции 5-20 мм | М3 | 6.345
С412-1283-4 | | | Щебень из природного камня для строительных работ марки 400, фракции 40-80 мм | М3 | 23.5
С412-1500 | | | Песок для строительных работ природный высшего класса | М3 | 31.0066
С412-4041 | | | Смеси асфальтобетонные (горячие) щебеночные мелкозернистые тип а, марки i | Т | 4.601082
С412-9005 | | | Вода | М3 | 4.28899
С414-1003 | | | Бетон тяжелый с крупностью заполнителя 20-40 мм, класса в7,5 | М3 | 3.3165
С414-2002 | | | Растворы кладочные тяжелые цементные, марки 50 | М3 | 0.6633
С414-2004 | | | Растворы кладочные тяжелые цементные, марки 100 | М3 | 0.1581
Составил _ _ _ _ _ _ _ _ _ _ _ _ _ _ _ _ / ______________ / | Проверил _ _ _ _ _ _ _ _ _ _ _ _ _ _ _ _ / ______________ /
