AliakseiHryhoryeu/graduate-work-construction-engineer/5. Экономика/Курсовой/Титульники.docx

Межгосударственное образовательное учреждение высшего образования

«Белорусско-Российский университет»

Кафедра: «Экономка и управление»

Курсовая работа

По дисциплине «Экономика производства»

На тему: «Сметно-финансовые расчёты»

Выполнил: студент гр.ПГС-171

Григорьев А.В.

Руководитель:

Макаревич О.Д.

Могилев 2020
