AliakseiHryhoryeu/graduate-work-construction-engineer/6. Охрана труда/Мое/Пояснительная Охрана труда.docx

6 Охрана труда

## 6.1 Идентификация и анализ вредных и опасных факторов при проектировании гостиницы на 152 номера в г. Минске

Идентификация вредных и опасных производственных факторов произведена в соответствии с ГОСТ 12.0.003-74. При этом выделены физические, химические, биологические и психофизические факторы, а также элементы, которые являются источниками возникновения этих факторов в проектируемом объекте.

Физические опасные и вредные производственные факторы:

¾ движущиеся машины и механизмы – бульдозер ДЗ-28, экскаватор ЭО-4321Б, башенный кран КС-503А.3, бетононасос Cila K20L, штукатурная станция Салют 2, использоваться копровая установка СП49Д с дизель-молотом С-966;

¾ повышенная запыленность и загазованность воздуха рабочей зоны – отделочные, электросварочные, бетонные, антикоррозийные работы;

¾ повышенная или пониженная температура поверхностей оборудования, материалов (отделочные, электросварочные, антикоррозийные работы, кровельные работы, приготовление бетонной смеси);

¾ повышенная или пониженная температура воздуха рабочей зоны (строительные работы в зимних условиях на открытом воздухе, работы в закрытых кабинах строительных машин, отделочные работы);

¾ повышенное значение напряжения в электрической цепи, замыкание которой может произойти через тело человека (земляные работы, бетонные работы, монтажные работы, электросварочные работы, освещение стройплощадки);

¾ повышенный уровень шума на рабочем месте создают двигатели автотранспортных средств, воздушных компрессоров и грузоподъемных кранов, грузоподъемные лебедки, пульверизаторы-распылители красок, пневматические молотки, пескоструйные аппараты;

¾ повышенный уровень вибрации вызывают пневматические молотки, ручные инструменты, а также передвижные машины и механизмы;

¾ расположение рабочего места на значительной высоте относительно поверхности земли (пола) – при монтаже конструкций каркаса.

Химические факторы:

Опасность химического воздействия существует в воздухе, и рабочие подвергаются ей воздушным путем через пыль, дым, туман, пары или газы (токсические выбросы в ходе сварочных работ). Следовательно, воздействие на человека осуществляется путем ингаляции, хотя некоторые частицы, переносимые воздушно-капельным путем, могут оседать на здоровую кожу и проникать в подкожный слой (органические растворители). Химическая опасность также возникает в результате с контактами с жидкими или полужидкими веществами (клеи и смолы) или порошками (сухой цемент). Накожный контакт с химическими веществами в таком агрегатном состоянии, часто сопровождается и возможным вдыханием паров, что обычно заканчивается общим отравлением организма или контактным дерматитом. Химические вещества могут попадать в организм с пищей или водой или путем ингаляции при курении.

Со строительными профессиями связаны заболевания:

¾ бронхит среди сварщиков;

¾ аллергии кожи среди каменщиков и рабочих других специальностей, работающих с цементом;

¾ неврологические расстройства среди маляров и рабочих других специальностей, контактирующих с органическими растворителями и свинцом.

Биологические опасные и вредные производственные факторы связаны с возможным воздействием инфекционных микроорганизмов, токсических веществ биологического происхождения и укусами животных.

Рабочие на земляных работах могут заболеть гистоплазмозом, инфекционным заболеванием легких, вызываемым почвенным грибком. Поскольку на строительном объекте постоянно происходит контакт между рабочими, то высока вероятность заболеть заразными заболеваниями, например, такими, как грипп или туберкулез.

Ядовитые вещества растительного происхождения находятся на листьях борщевика Сосновского и крапивы. Все они могут вызвать кожную сыпь.

Укусы животных бывают редко, но они случаются, когда соседство со стройплощадкой начинает беспокоить их или угрожает разрушить их среду обитания. Угроза укусов обычно происходит от ос, шершней, муравьев, змей и многих других видов.

Психофизиологические опасные и вредные производственные факторы:

¾ физические перегрузки;

¾ нервно-психические перегрузки.

Физические перегрузки:

¾ статические;

¾ динамические.

Статические перегрузки вызываются длительным пребыванием человека в вынужденной рабочей позе или длительным статическим напряжениям отдельных групп мышц при выполнении работ, например, при сварочных работах.
Динамические перегрузки вызываются большим количеством стереотипных движений за короткий промежуток времени (погрузочно-разгрузочные работы, подъем и переноска приспособлений).

Нервно-психические перегрузки:

¾ умственное перенапряжение;

¾ перенапряжение анализаторов;

¾ монотонность труда;

¾ эмоциональные перегрузки.

Нервно-эмоциональное перенапряжение может быть вызвано ответственностью за выполняемую работу, высокими требованиями к качеству, сложностью или необычностью работы, особенно в условиях дефицита времени. Нервно-эмоциональное напряжение может нарушить функциональное состояние сердечно-сосудистой и центральной нервной системы.

Один и тот же опасный и вредный производственный фактор по природе своего действия может относиться одновременно к различным группам, перечисленным выше.

Строительные процессы на строительной площадке происходят на открытом воздухе, что затрудняет создание и поддержание параметров климатических условий на рабочих местах. Работа на объекте в две смены создает особую опасность для работающих, в особенности в условиях недостаточной освещенности. Эти факторы действуют на человека суммарно, ослабляя или усиливая друг друга.

При проведении земляных работ возможен обвал грунта, падение рабочих в котлован, обрушение бровки из-за неправильной привязки землеройно-транспортных машин и механизмов.

При монтажных работах вместе с факторами, указанными выше, представляет опасность ведение одновременно с монтажом других видов работ.

На строительной площадке имеются зоны опасных производственных факторов – площадки монтажа, площадки вблизи технологических проемов в перекрытии. В этих местах существует наибольшая вероятность механических повреждений: падение человека с высоты, падение конструкций на человека.

В местах повреждения изоляции в следствие механического воздействия или от воздействия химически агрессивной среды на корпусах строительных машин может появится напряжение, что вызывает при соприкосновении с ними электрический удар или травму.

При производстве отделочных работ существует опасность отравления вредными газами и парами. При производстве наружной окраски и отделке фасада существует опасность выпадение рабочих из люлек. Так же представляет собой опасность работа с ручным электроинструментом.

При кровельных работах, при производстве работ возможно падение рабочих из-за отсутствия средств индивидуальной защиты.

Общие для всех работ – несоблюдение правил охраны труда, а также правил эксплуатации строительных машин и механизмов.

6.2 Технические, технологические, организационные решения по устранению вредных и опасных факторов. Разработка защитных средств

Организация строительной площадки, участков работ и рабочих мест обеспечивает безопасность труда на всех этапах выполнения работ в соответствие с ТКП 45-1.03-40-2006 и ТКП 45-1.03-44-2006. Все опасные зоны имеют сигнальные ограждения и знаки, согласно ГОСТ 12.4.026-2015. Конструкция ограждения площадки

соответствуют требованиям ГОСТ 12.4.026-2015. Проезды, проходы имеют освещение в соответствии с ТКП 45-2.04-153-2009. Колодцы и шурфы закрываются крышками и ограждаются.

Эксплуатация строительных машин осуществляется в соответствии с требованиями ГОСТ 12.2.061-81 и ГОСТ 12.3.033-84. В зоне работы машины установлены предупредительные знаки. При применении ручных машин руководствуются требованиями ГОСТ 12.2.007.13-2000.

У въезда на площадку установлена схема движения транспорта. Входы в здание защищены сплошным навесом. Оконные проемы ограждаются в соответствии с ГОСТ 12.4.059-89.

Земляные работы. Грунт, извлеченный из котлована, размещается на расстоянии не менее 0,5 метра от бровки. Грунт разрабатывается сверху вниз. Погрузка грунта в транспортное средство осуществляется со стороны бокового борта. Для подъема и спуска рабочих в котлован применяются трапы шириной 0,6 метра с перилами.

Погрузо-разгрузочные работы. Площадка для этих работ планируется и имеет уклон не более пяти градусов. Установлены надписи “Въезд”, “Выезд”, “Разворот”. При перемещении грузов в таре и хрупких материалов необходимо исключать толчки и удары.

Электросварочные работы. Выполняются в соответствии с ГОСТ 12.3.003-86*, ГОСТ 12.3.036-84. Места производства сварочных работ освобождаются от сгораемых материалов в радиусе не менее пяти метров, сварочный аппарат имеет изоляцию и заземление. Электросварочные работы во время дождя вне навесов не выполняются.

Кровельные работы. Допуск рабочих к выполнению работ разрешается выполнять в соответствии с требованиями ГОСТ 12.3.040-86. Рабочие обеспечиваются поясами по ГОСТ 12.4.089-86. Размещение на крыше материалов для производства кровельных работ допускается только в местах, предусмотренных проектом производства работ, с применением мер против их падения, в т. ч. от воздействия ветра.

Отделочные работы. Подмости, применяемые при штукатурных и малярных работах в местах, где есть проход, имеют настил без зазоров. При производстве штукатурных работ обеспечивается двухсторонняя связь между оператором и машинистом штукатурной станции.

При производстве малярных работ необходимо руководствоваться требованиями ГОСТ 12.3.035-84 .

Электробезопасность машин выполняется в соответствии с ГОСТ 12.1.001-89, ГОСТ 12.1.006-84 .

При производстве комплекса СМР, средства индивидуальной защиты соответствуют требованиям, предъявляемым ГОСТ 12.4.011-89. Все санитарно-бытовые помещения рассчитаны на определенное количество рабочих. На объекте специально предусмотрено помещение для хранения медикаментов. Все работающие проходят инструктаж по технике безопасности в установленные сроки.’

Пожаробезоспасность осуществляется в соответствии с Декретом Президента РБ №7 от 23.11.2017, СН 2.02.03-2019, СТБ 11.0.02-95.

Для обеспечения безопасности на строительной площадке в темное время суток предусмотрены прожекторы охранного, общего и локального пользования. Прожекторы показаны на листе стройгенплана графической части.

Каменные конструкции благодаря своей массивности и теплофизическим свойствам обладают хорошим сопротивлением действию огня. В условиях пожара высоким пределом огнестойкости обладают бетоны, которые выдерживают нагрев до 9000С, почти не снижая своей прочности и не обнаруживая признаков разрушения.

Железобетонные конструкции благодаря их сравнительно небольшой теплопроводности довольно хорошо сопротивляются воздействию агрессивных факторов пожара. Но они не могут беспредельно сопротивляться воздействию пламени. Наиболее часто пожары возникают из-за: нарушений правил сварочных работ; применения открытого огня для обогрева коммуникаций, двигателей; курения в запретных местах; короткого замыкания в электропроводах.

На строительной площадке пожаротушение обеспечивается пожарными гидрантами и водопроводом. Места размещения пожарных гидрантов показаны на стройгенплане.

На территории стройплощадки устанавливается бочки с водой, противопожарный щит, ящик с песком, огнетушитель.

6.3 Разработка мер безопасности при строительстве и эксплуатации объекта проектирования

Разработана инструкция по охране труда для бетонщика (Приложении Б).

923/21-ПЗ Лист Изм. Кол. Лист №док. Подпись Дата
