AliakseiHryhoryeu/graduate-work-construction-engineer/2. Расчетно-конструктивный раздел/Пример/2/plita_raschet_iz_robota.rtf

1. Плита: Плита28 - Плита № 28

1.1. Армирование:

• Тип : ЖБ перекрытие
• Направление рабочей арматуры : 0°
Основной класс арматуры : Нормативная прочность = 500,00 МПа
Горизонтальная ветвь графика зависимости напряжений от деформации
• Класс пластичности : C
• Диаметры стержней нижняя d1 = 1,6 (см) d2 = 1,6 (см)
верх d1 = 1,6 (см) d2 = 1,6 (см)
• Защитный слой нижняя c1 = 3,0 (см)
верх c2 = 3,0 (см)
• Отклонения защитного слоя Cdev = 1,0(см), Cdur = 0,0(см)

1.2. Бетон

Класс : C25/30; Нормативная прочность = 25,00 МПа
Прямоугольное распределение напряжений [3.1.7(3)]
• Плотность : 2501,36 (кГ/м3)
• Коэффициент ползучести бетона : 1,53
• Марка цемента : N

1.3. Гипотеза

• Расчеты по : EN 1992-1-1:2004/A1:2014
• Методы расчета площади арматуры : аналитический
• Допустимая ширина раскрытия трещин
- верхний слой : 0,40 (мм)
- нижний слой : 0,40 (мм)
• Допустимый прогиб : 3,0 (см)
• Проверка продавливания : да
• Внешние воздействия
- верхний слой : X0
- нижний слой : X0
• Тип расчета : чистый изгиб
• Класс конструкции : S1

1.4. Геометрия пластины

Толщина 0,30 (м)

Контур:
ребро начало конец длина
x1 y1 x2 y2 (м)
1 31,44 -18,19 31,44 -16,84 1,34
2 31,44 -16,84 41,07 -16,84 9,63
3 41,07 -16,84 41,07 -10,97 5,88
4 41,07 -10,97 42,52 -10,97 1,45
5 42,52 -10,97 42,52 -5,83 5,14
6 42,52 -5,83 40,97 -5,83 1,56
7 40,97 -5,83 40,97 0,15 5,98
8 40,97 0,15 33,82 0,15 7,15
9 33,82 0,15 33,82 1,75 1,60
10 33,82 1,75 30,67 1,75 3,15
11 30,67 1,75 30,67 1,45 0,30
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
10,05 18,28 14,36 18,28
Измененное теоретическое армирование (см2/м):
9,64 4,52 12,82 4,52
Первоначальное теоретическое армирование (см2/м):
9,64 4,52 12,82 4,52
Координаты (м):
33,82;-7,35 15,21;-4,36 34,50;-15,50 15,21;-4,36

1.5.2. Максимальные моменты + армирование при изгибе

Ax(+) Ax(-) Ay(+) Ay(-)

Символ: теоретическая площадь/фактическая площадь
Ax(+) (см2/м) 9,64/10,05 0,00/5,03 8,33/10,05 0,00/5,03
Ax(-) (см2/м) 0,00/15,96 4,52/18,28 0,00/18,28 4,52/18,28
Ay(+) (см2/м) 5,42/14,36 0,00/4,79 12,82/14,36 0,00/4,79
Ay(-) (см2/м) 0,00/18,28 4,52/18,28 0,25/18,28 4,52/18,28

ПС2
Mxx (кН*м/м) 26,88 -6,80 32,87 -6,80
Myy (кН*м/м) 15,82 -5,06 26,49 -5,06
Mxy (кН*м/м) -3,10 0,45 1,31 0,45

Nxx (кН/m) -24,30 -2,99 -8,19 -2,99
Nyy (кН/m) -27,40 -3,61 17,14 -3,61
Nxy (кН/m) -0,48 1,45 0,62 1,45

ПС1
Mxx (кН*м/м) 37,72 -9,54 46,13 -9,54
Myy (кН*м/м) 22,20 -7,10 37,17 -7,10
Mxy (кН*м/м) -4,35 0,63 1,83 0,63

Nxx (кН/m) -34,08 -4,20 -11,49 -4,20
Nyy (кН/m) -38,41 -5,06 24,05 -5,06
Nxy (кН/m) -0,68 2,03 0,87 2,03

Координаты (м) 33,82;-7,35 15,21;-4,36 34,50;-15,50 15,21;-4,36
Координаты* (м) 7,15;7,50;3,00 25,76;4,51;3,00 6,47;15,65;3,00 25,76;4,51;3,00
* - Координаты в общей системе координат конструкции

1.5.3. Продавливание

Опора № / Точка Расположение (м) Геометрия: (м)
x y a b d h
P1 0,00 0,00 Сила 0,50 0,50 - -

Опора № / Точка Нагрузки: (кН) Критический периметр (м)
Q Qadm u Qadm / Q

Опора № / Точка: P1
uo = @VAL(Data_p=Uo)@
u1 = @VAL(Data_p=U1)@
ρLx = @VAL(Data_p=RoLx)@
ρLy = @VAL(Data_p=RoLy)@
heff = @V_U(Data_p=EffHeight)@
Ax = @V_U(Data_p=Ax)@
Ay = @V_U(Data_p=Ay)@
α = @VAL(Data_p=Alpha)@
ν = @V_U(Data_p=Ni)@
γc = @V_U(Data_p=Gamma_c)@
fcd = @V_U(Data_p=Fcd)@
vRdmax = @V_U(Data_p=VRdmax)@

vRdc = @VAL(Data_p=VRdc)@
νmin = @VAL(Data_p=Ni_min)@
vEds = @VAL(Data_p=VEds)@
cRdc= @VAL(Data_p=CRdc)@
k = @VAL(Data_p=K)@
ρL = @V_U(Data_p=RoL)@
vlim = @V_U(Data_p=StressLimit)@
v = @V_U(Data_p=Stress)@
A = @V_U(Data_p=ShearArea)@

1.5.4. Прогиб
|f(+)| = 0,0 (см) <= fdop(+) = 3,0 (см)
|f(-)| = 1,7 (см) <= fdop(-) = 3,0 (см)

1.5.5. Трещинообразование
верхний слой
ax = 0,36 (мм) <= adop = 0,40 (мм)
ay = 0,37 (мм) <= adop = 0,40 (мм)
нижний слой
ax = 0,00 (мм) <= adop = 0,40 (мм)
ay = 0,38 (мм) <= adop = 0,40 (мм)

2. Нагрузки:

Вариант Тип Список Значение
1 собственный вес 28до98 PZ Отрицательный
2 (КЭ) равномерно распределенная 28 PZ=-0,21(кН/м2)
3 (КЭ) равномерно распределенная 28 PZ=-2,83(кН/м2)

Сочетание/Компонента Назначение

3. Результаты - деталировка

Список решений:
Армирование: стержни
Решение № Пределы армирования Общий вес
Диаметр / Вес (кГ)
1 - 28110,47

Результаты для решения № 1
Зоны армирования

Нижняя арматура
Имя координаты Фактическая арматура At Ar
x1 y1 x2 y2 φ (мм) / (см) (см2/м) (см2/м)
1/1- Основная Ax 0,00 -19,19 42,52 1,85 16,0 / 11,0 4,52 < 18,28
1/2- Перпендикулярная Ay 0,00 -19,19 42,52 1,85 16,0 / 11,0 4,52 < 18,28

Верхняя арматура
Имя координаты Фактическая арматура At Ar
x1 y1 x2 y2 φ (мм) / (см) (см2/м) (см2/м)
1/1+(1/31+) Основная Ax 0,00 -16,84 4,44 -15,01 16,0 / 20,0 6,31 < 10,05
1/2+(1/31+) Основная Ax 0,00 -6,53 2,66 -3,40 16,0 / 20,0 5,81 < 10,05
1/3+(1/31+) Основная Ax 8,74 -12,26 15,59 -10,40 16,0 / 20,0 9,13 < 10,05
1/4+(1/31+) Основная Ax 12,70 -16,84 21,48 -14,09 16,0 / 20,0 7,62 < 10,05
1/5+(1/31+) Основная Ax 19,49 -13,17 27,52 -10,40 16,0 / 20,0 8,11 < 10,05
1/6+(1/31+) Основная Ax 29,36 -12,26 32,23 -10,09 16,0 / 20,0 5,67 < 10,05
1/7+(1/31+) Основная Ax 32,23 -7,85 35,55 -2,55 16,0 / 20,0 9,64 < 10,05
1/8+(1/31+) Основная Ax 33,82 -16,84 35,55 -15,01 16,0 / 20,0 8,33 < 10,05
1/9+(1/31+) Основная Ax 38,26 -4,25 40,97 -1,70 16,0 / 20,0 5,40 < 10,05
1/10+(1/31+) Основная Ax 0,00 -16,84 1,78 -0,00 16,0 / 40,0 4,52 < 5,03
1/11+(1/31+) Основная Ax 1,78 -16,84 41,07 -15,01 16,0 / 40,0 4,91 < 5,03
1/12+(1/31+) Основная Ax 1,78 -13,17 13,43 -0,00 16,0 / 40,0 4,90 < 5,03
1/13+(1/31+) Основная Ax 4,44 -15,01 41,07 -13,17 16,0 / 40,0 4,91 < 5,03
1/14+(1/31+) Основная Ax 6,46 -0,00 10,94 1,85 16,0 / 40,0 4,52 < 5,03
1/15+(1/31+) Основная Ax 9,89 -17,99 23,37 -16,84 16,0 / 40,0 4,80 < 5,03
1/16+(1/31+) Основная Ax 10,94 -0,00 40,97 0,15 16,0 / 40,0 4,90 < 5,03
1/17+(1/31+) Основная Ax 13,43 -13,17 41,07 -6,60 16,0 / 40,0 4,76 < 5,03
1/18+(1/31+) Основная Ax 13,43 -4,25 30,23 -0,00 16,0 / 40,0 4,52 < 5,03
1/19+(1/31+) Основная Ax 15,59 -6,60 30,23 -4,25 16,0 / 40,0 4,52 < 5,03
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
16 7,87 3
16 7,89 1
16 7,90 4
16 7,93 3
16 7,94 15
16 8,05 17
16 8,11 10
16 8,14 12
16 8,16 2
16 8,25 3
16 8,27 8
16 8,29 2
16 8,30 7
16 8,33 7
16 8,48 1
16 8,50 102
16 8,52 144
16 8,54 3
16 8,58 10
16 8,62 3
16 8,63 4
16 8,64 30
16 8,66 4
16 8,70 4
16 8,82 153
16 8,84 180
16 8,86 4
16 8,95 2
