AliakseiHryhoryeu/graduate-work-construction-engineer/2. Расчетно-конструктивный раздел/Пример/2/zapiska.docx

2 Расчетно – конструктивный раздел

2.1 Расчет и конструирование перекрытия кровли в монолитном

железобетоне

Дипломный проект выполнен в монолитном железобетонном исполнении и включает в себя расчет и конструирование программным методом монолитного перекрытия. Расчет выполняется с применением программ Autodesk Robot Structural Analysis Professional 2021 путем интеграции 3D модели проекта из Autodesk Revit 2021. Результаты расчета и армирования экспортируются в изначальную модель для формирования необходимых чертежей.

Таблица 2.1 – Исходные данные

Тип здания | Гражданское
Размер здания в плане А х Б | 14,2х21,58 м
Количество этажей n1 | 25
Высота этажа Н1 | 3,9 м
Район строительства | г.Минск
Снеговая нагрузка S0 | 1,87 кПа

Таблица 2.2 – Характеристики материалов монолитного варианта

Конструкция | Класс бетона | Класс рабочей арматуры
Плита | С25/30 | S500

2.2 Подсчет нагрузок на плиту

Таблица 2.3 Нагрузки на плиту покрытия
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
