AliakseiHryhoryeu/graduate-work-construction-engineer/1. Архитектура/фото/45.png

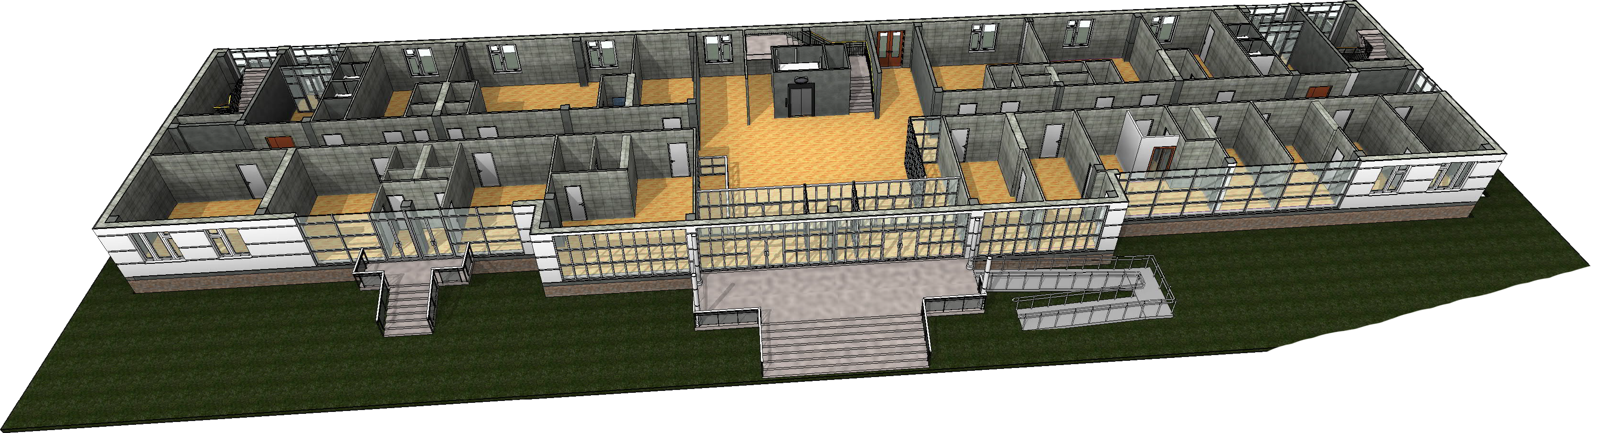
1. Архитектура/фото/45.png
