AliakseiHryhoryeu/graduate-work-construction-engineer/1. Архитектура/фото/1113D разрезы.png

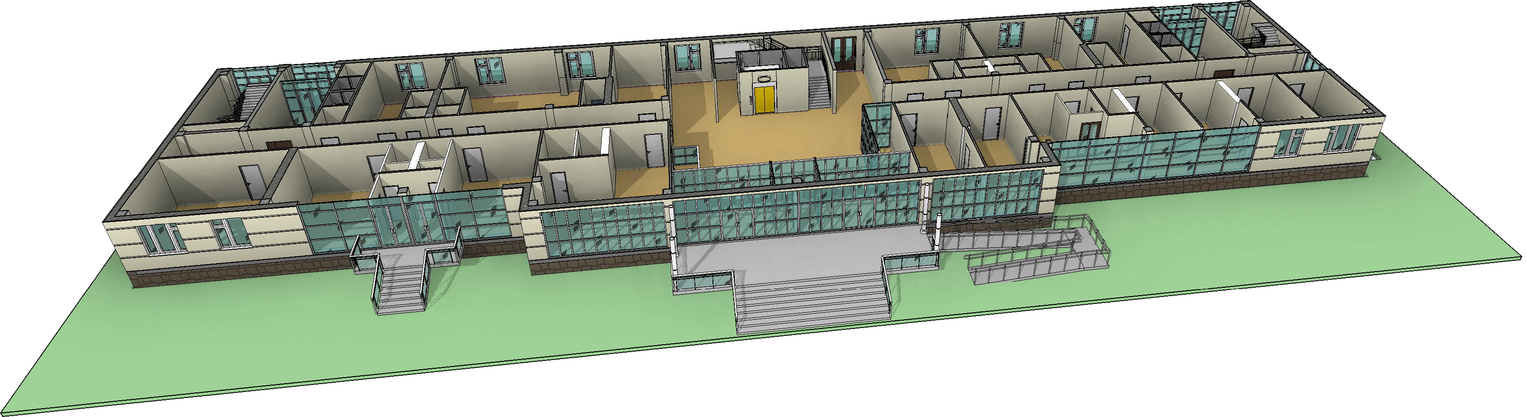
1. Архитектура/фото/1113D разрезы.png
