AliakseiHryhoryeu/graduate-work-construction-engineer/1. Архитектура/фото/31523617.png

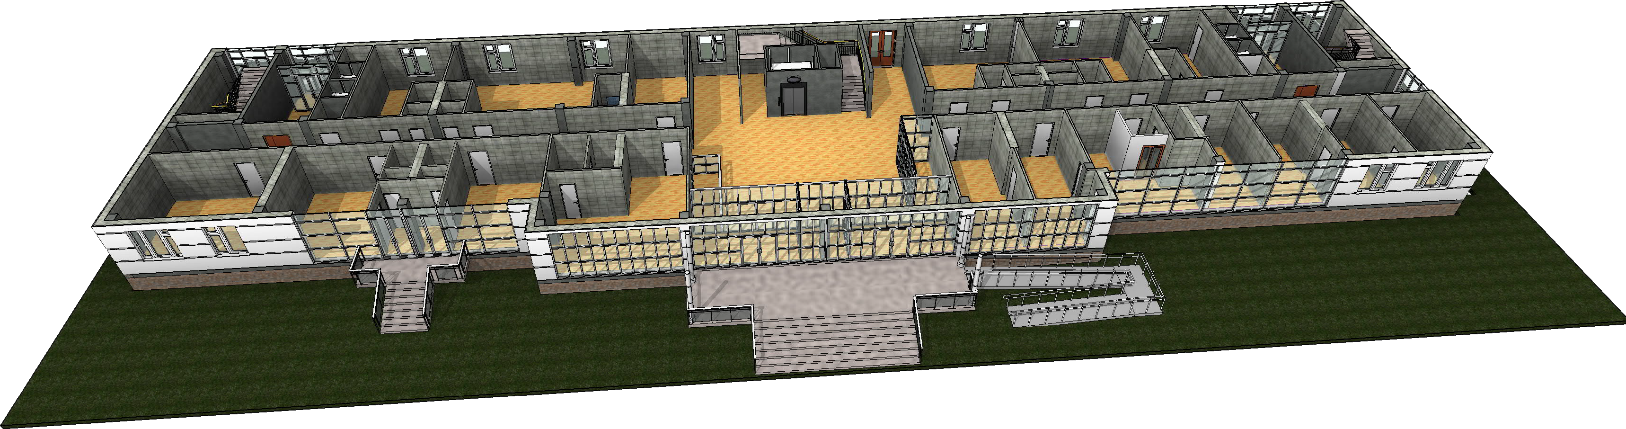
1. Архитектура/фото/31523617.png
