AliakseiHryhoryeu/graduate-work-construction-engineer/1. Архитектура/фото/наружняя стена.jpg

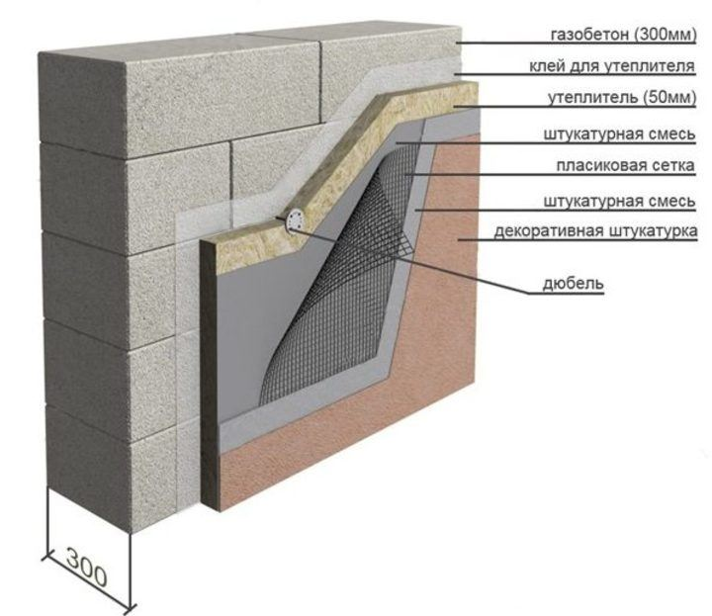
1. Архитектура/фото/наружняя стена.jpg
