AliakseiHryhoryeu/graduate-work-construction-engineer/Задание/6fBKzHKOh2I.jpg

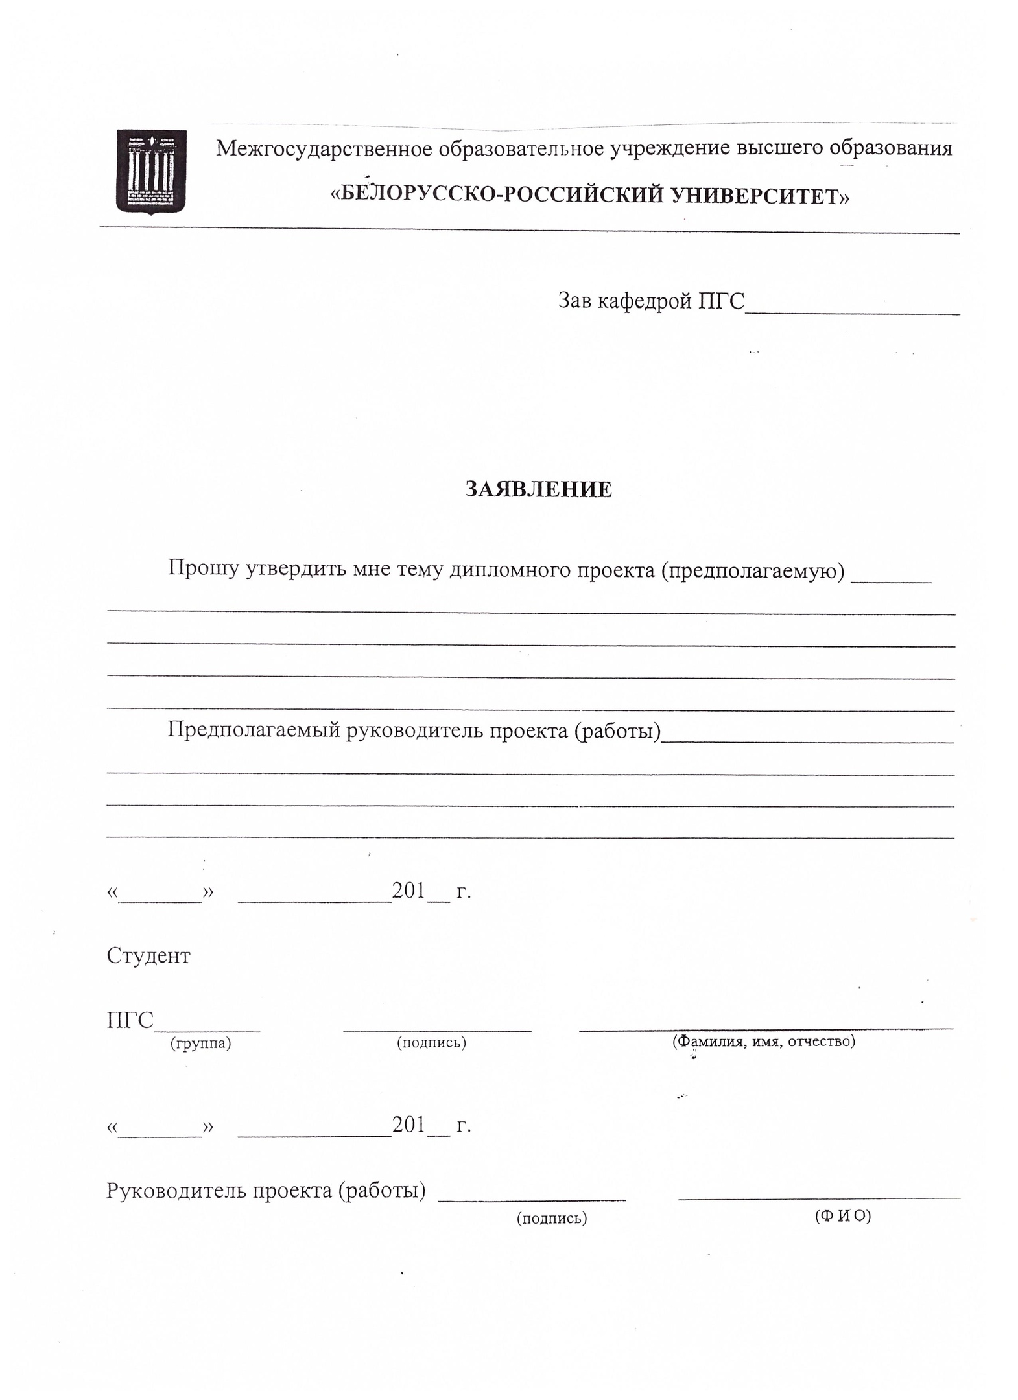
Задание/6fBKzHKOh2I.jpg
