AliakseiHryhoryeu/graduate-work-construction-engineer/Задание/11221.png

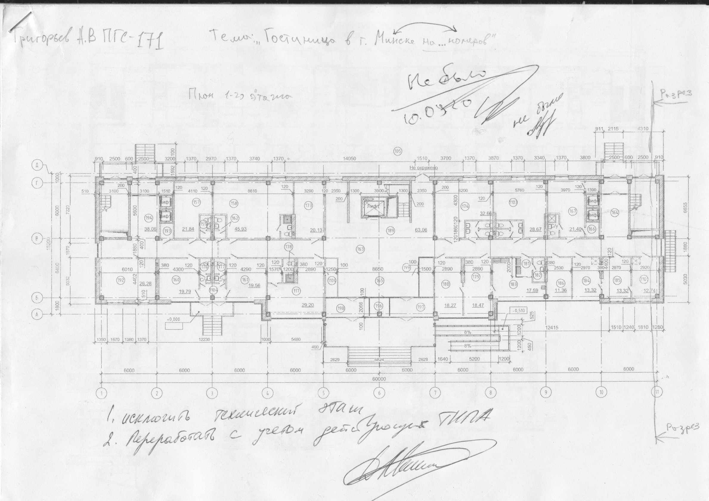
Задание/11221.png
