AliakseiHryhoryeu/graduate-work-construction-engineer/Задание/j4jczyIpAIQ.jpg

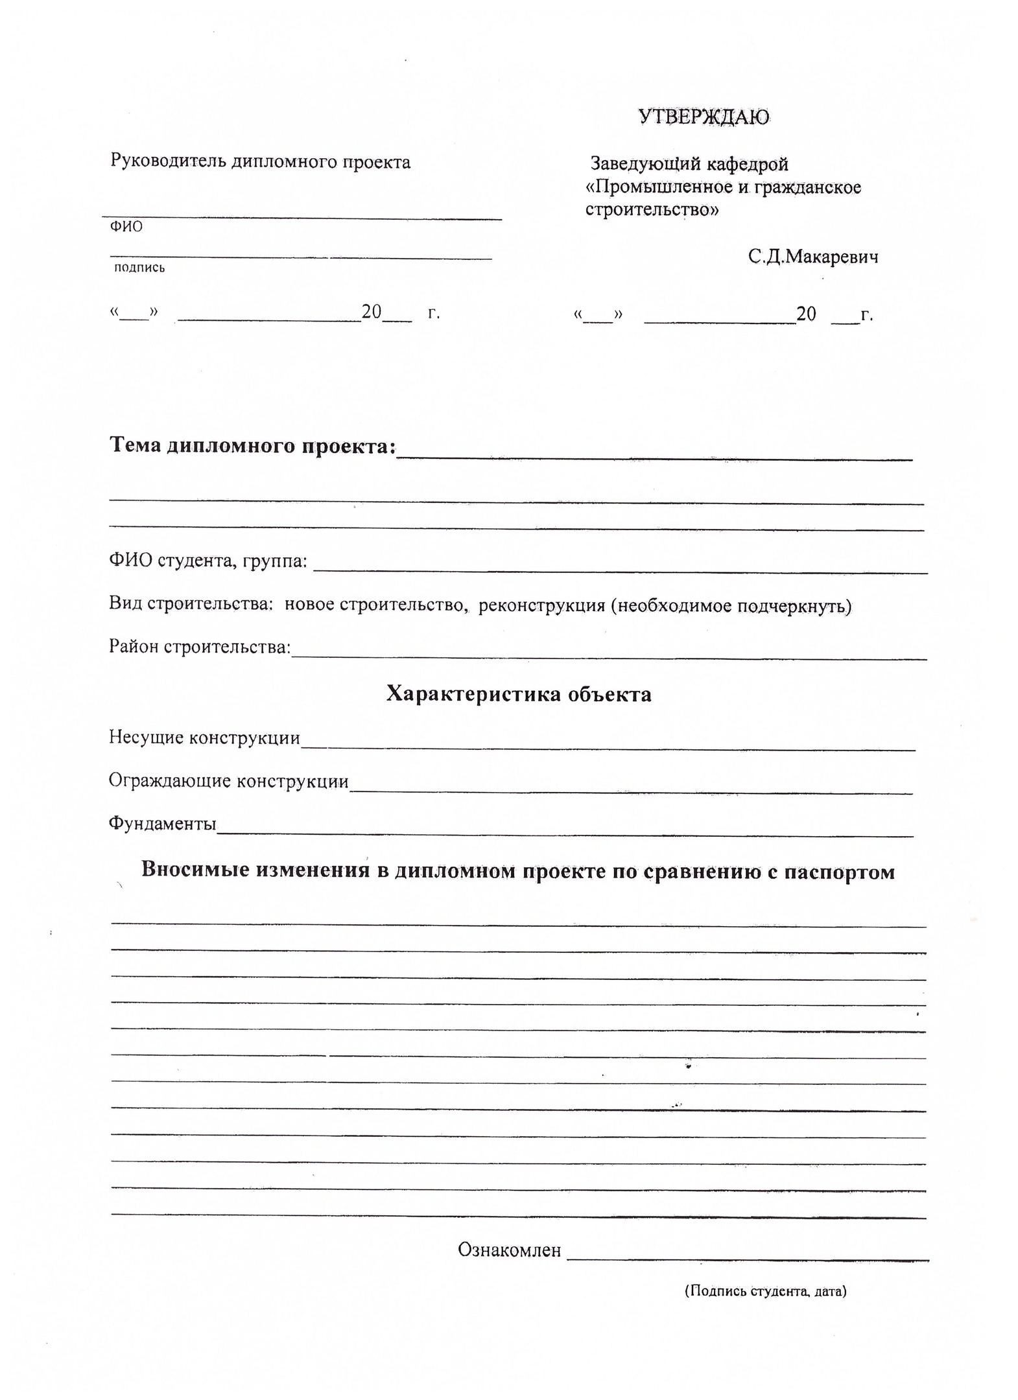
Задание/j4jczyIpAIQ.jpg
