AliakseiHryhoryeu/graduate-work-construction-engineer/Защита диплома/немного картинок/3d разрез Copy 1 Copy 1.jpg

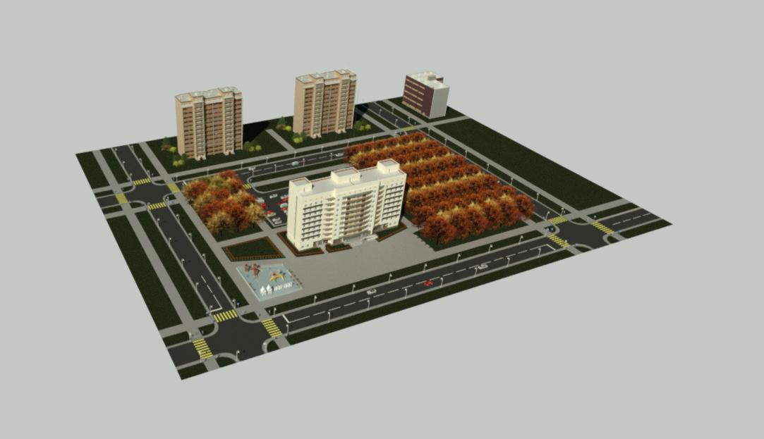
Защита диплома/немного картинок/3d разрез Copy 1 Copy 1.jpg
