AliakseiHryhoryeu/graduate-work-construction-engineer/Защита диплома/немного картинок/3d разрез.jpg

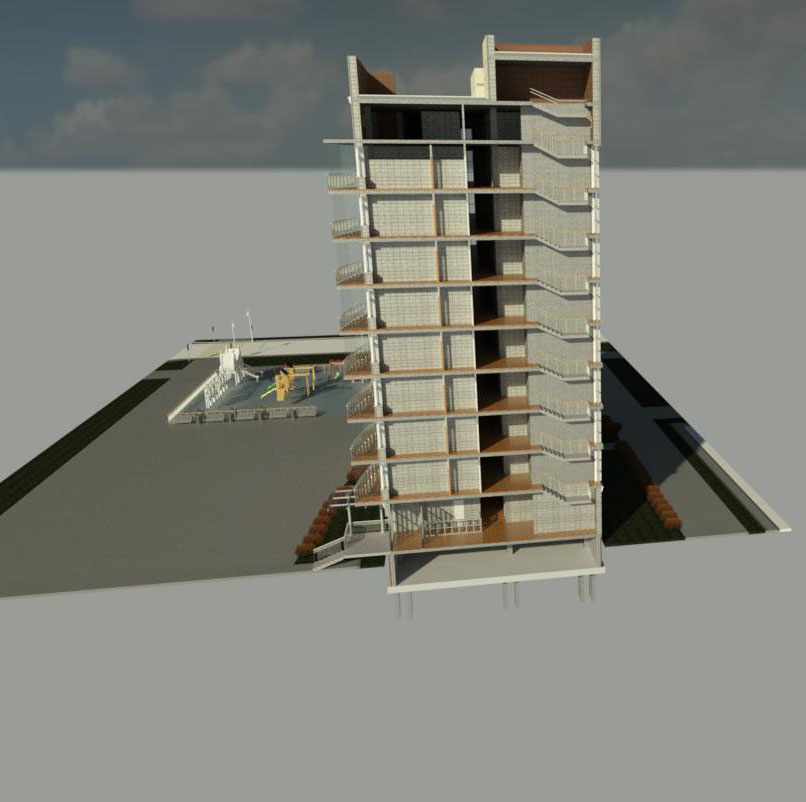
Защита диплома/немного картинок/3d разрез.jpg
