AliakseiHryhoryeu/graduate-work-construction-engineer/Защита диплома/немного картинок/2021-06-17_20-31-06.png

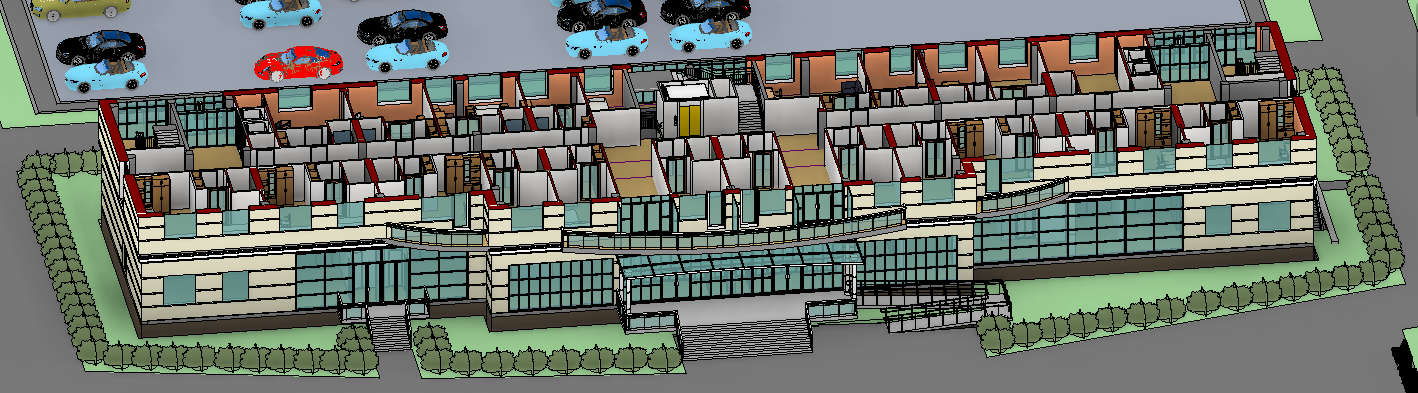
Защита диплома/немного картинок/2021-06-17_20-31-06.png
