AliakseiHryhoryeu/graduate-work-construction-engineer/Защита диплома/немного картинок/5484444884.jpg

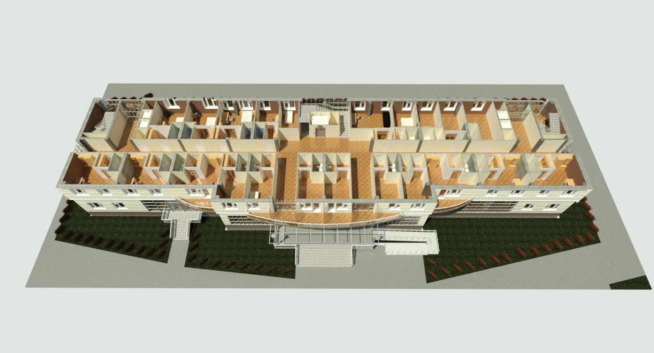
Защита диплома/немного картинок/5484444884.jpg
