AliakseiHryhoryeu/graduate-work-construction-engineer/Защита диплома/немного картинок/еуууыапыфа.jpg

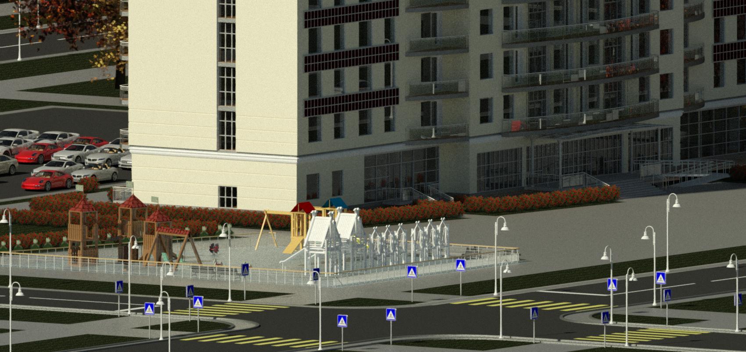
Защита диплома/немного картинок/еуууыапыфа.jpg
