AliakseiHryhoryeu/graduate-work-construction-engineer/Защита диплома/немного картинок/паолпоапо.png

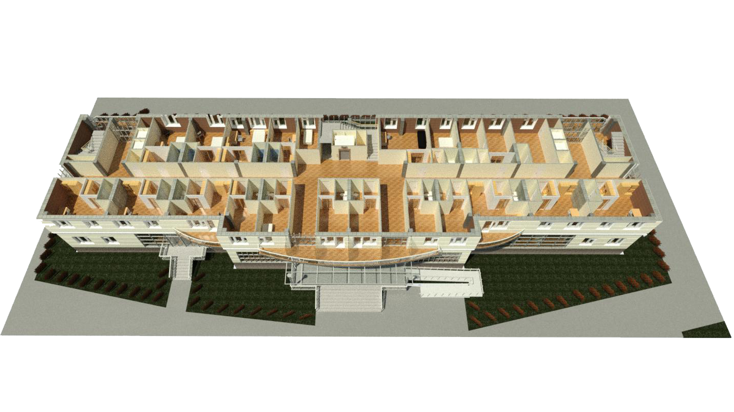
Защита диплома/немного картинок/паолпоапо.png
