AliakseiHryhoryeu/graduate-work-construction-engineer/Защита диплома/немного картинок/фыпфпыпф.jpg

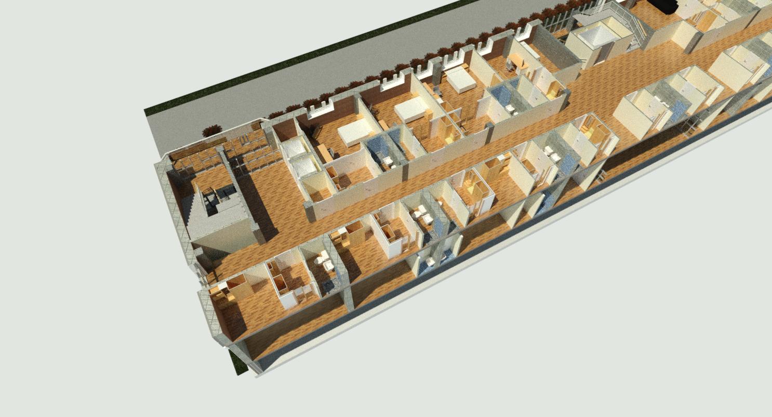
Защита диплома/немного картинок/фыпфпыпф.jpg
