AliakseiHryhoryeu/graduate-work-construction-engineer/Листы А1/2 3d разрез 1 этажа.png

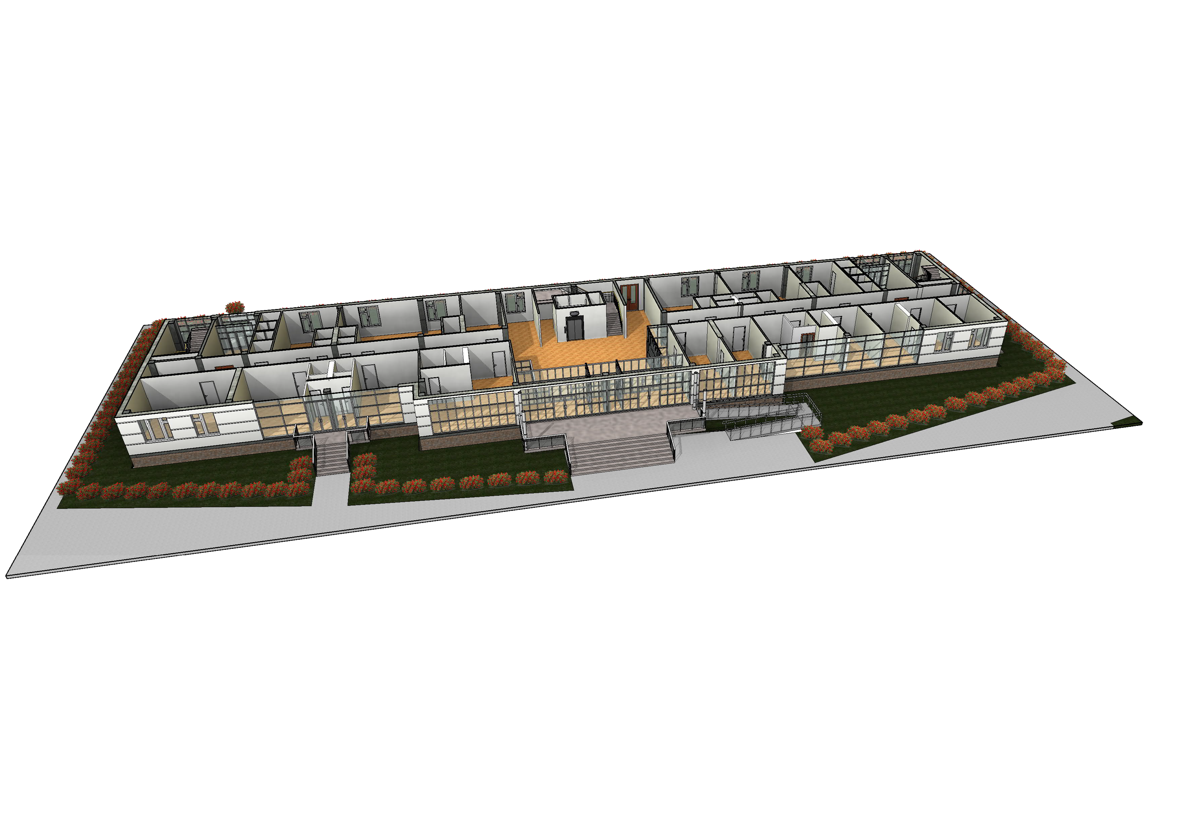
Листы А1/2 3d разрез 1 этажа.png
