AliakseiHryhoryeu/graduate-work-construction-engineer/Листы А1/3d схема опалубки.png

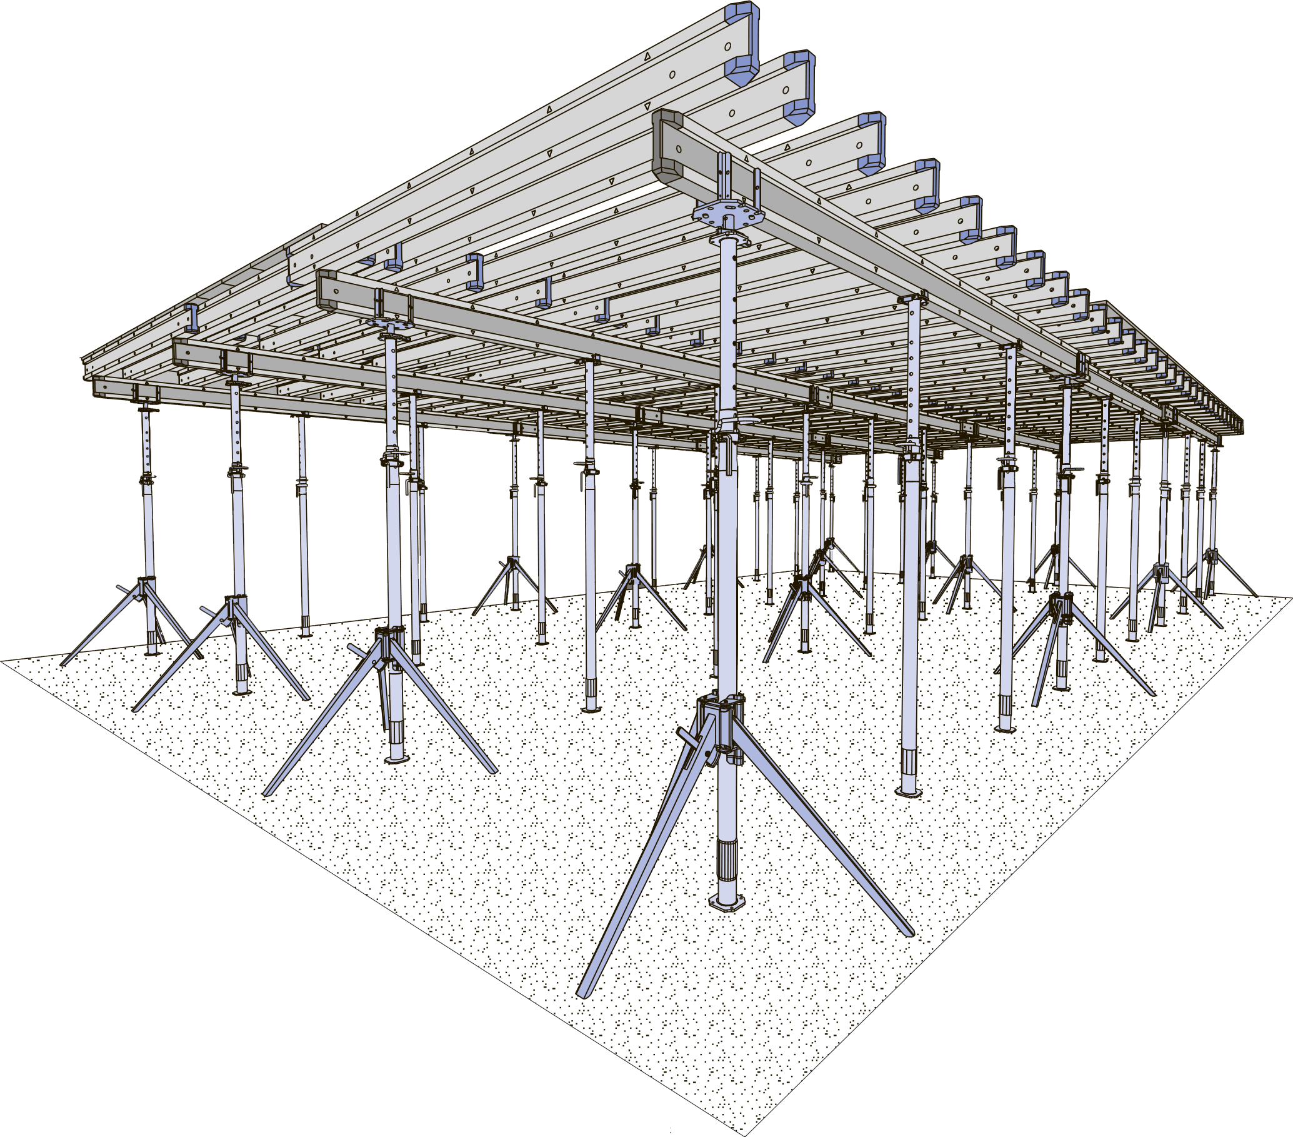
Листы А1/3d схема опалубки.png
