AliakseiHryhoryeu/graduate-work-construction-engineer/Листы А1/3стройгенплан.png

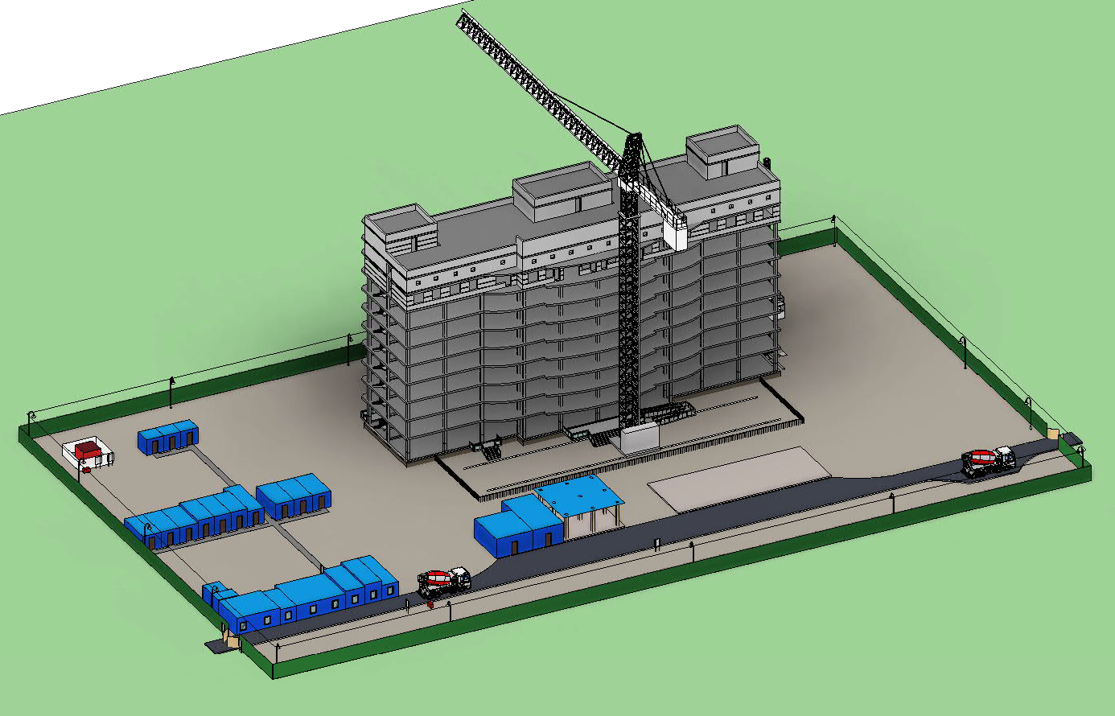
Листы А1/3стройгенплан.png
