AliakseiHryhoryeu/graduate-work-construction-engineer/Листы А1/1111стройгенплан.png

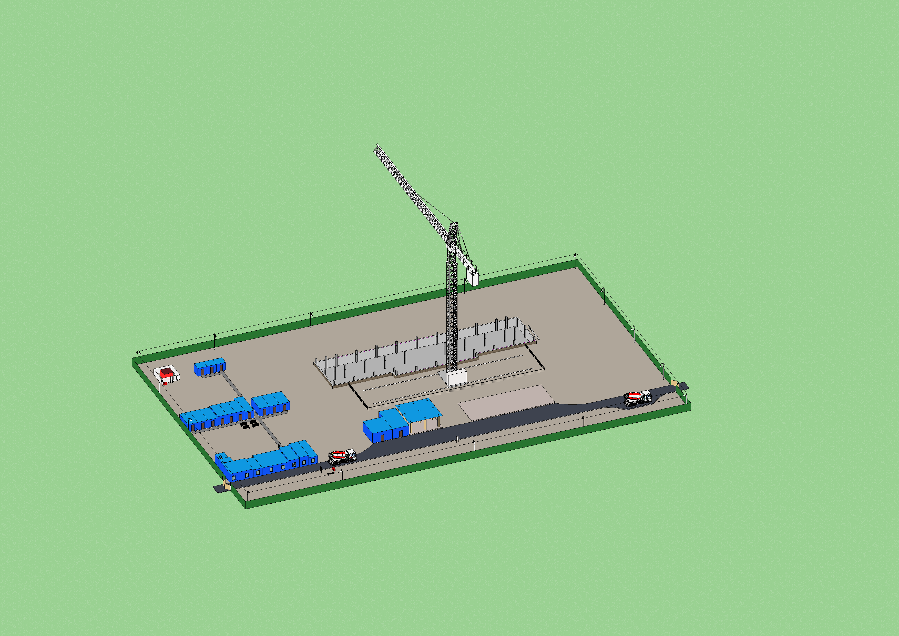
Листы А1/1111стройгенплан.png
