AliakseiHryhoryeu/graduate-work-construction-engineer/Листы А1/2021-05-06_20-32-28.png

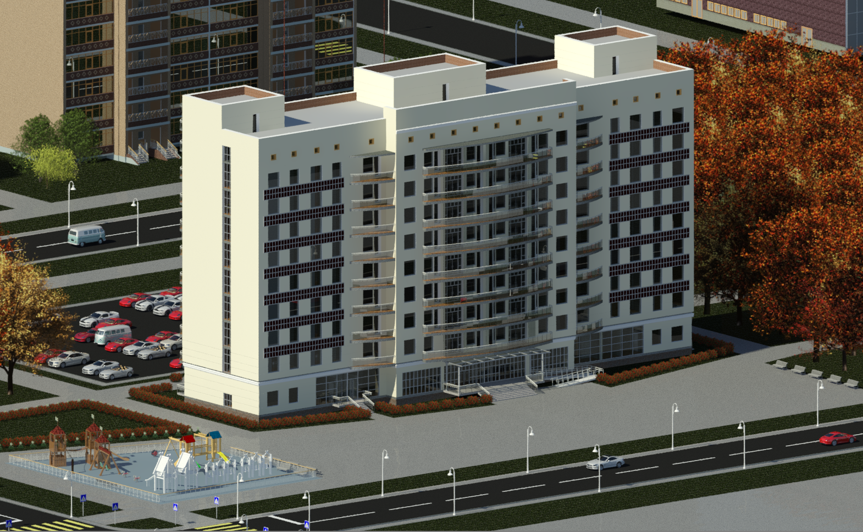
Листы А1/2021-05-06_20-32-28.png
