AliakseiHryhoryeu/graduate-work-construction-engineer/Листы А1/2021-05-23_12-32-26.png

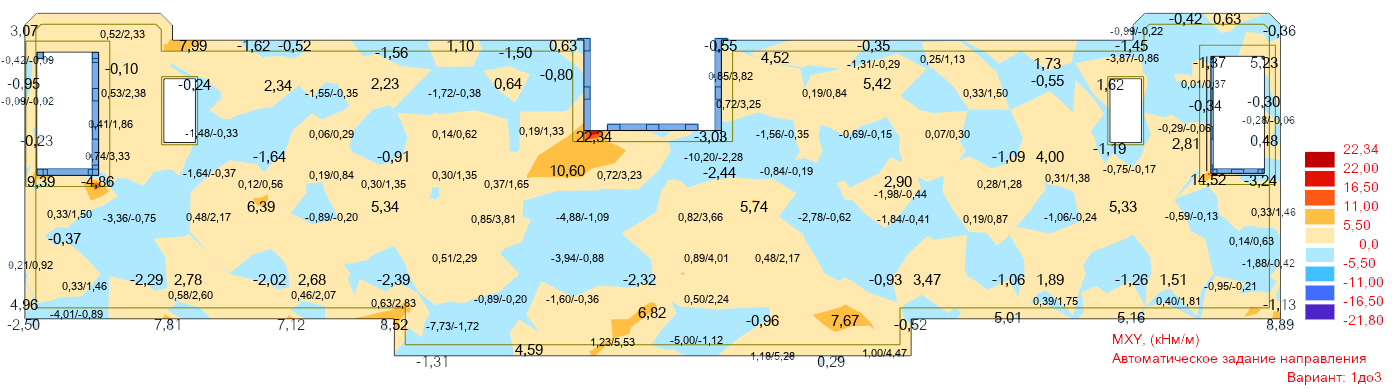
Листы А1/2021-05-23_12-32-26.png
