AliakseiHryhoryeu/graduate-work-construction-engineer/Листы А1/2222стройгенплан.png

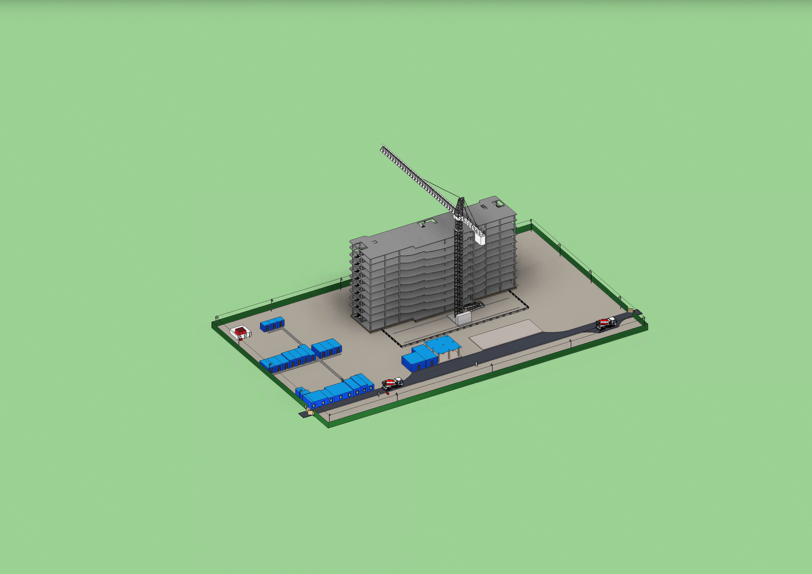
Листы А1/2222стройгенплан.png
