AliakseiHryhoryeu/graduate-work-construction-engineer/Листы А1/654546456.png

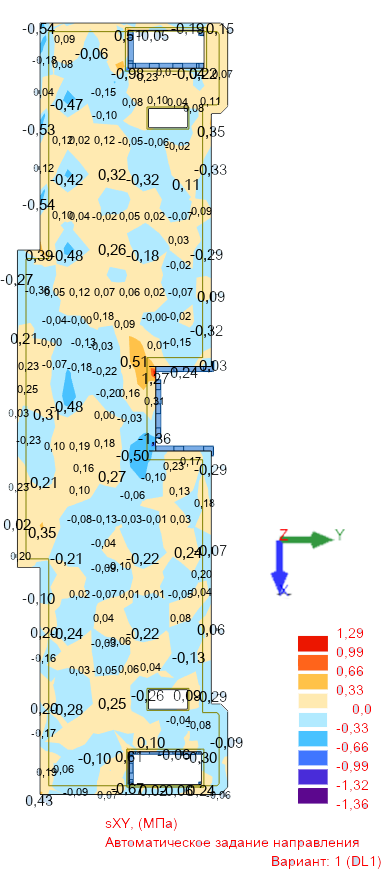
Листы А1/654546456.png
