AliakseiHryhoryeu/graduate-work-construction-engineer/Листы А1/33333333333.png

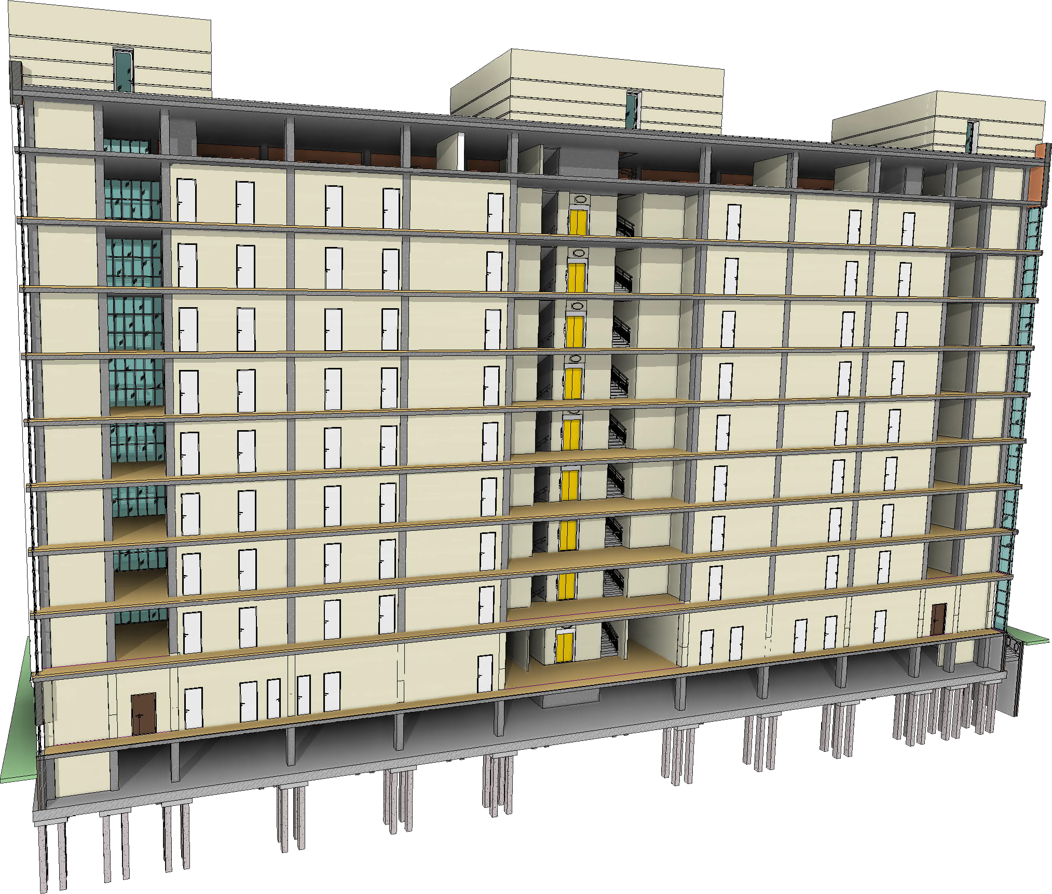
Листы А1/33333333333.png
