AliakseiHryhoryeu/graduate-work-construction-engineer/Листы А1/11111111111111113.png

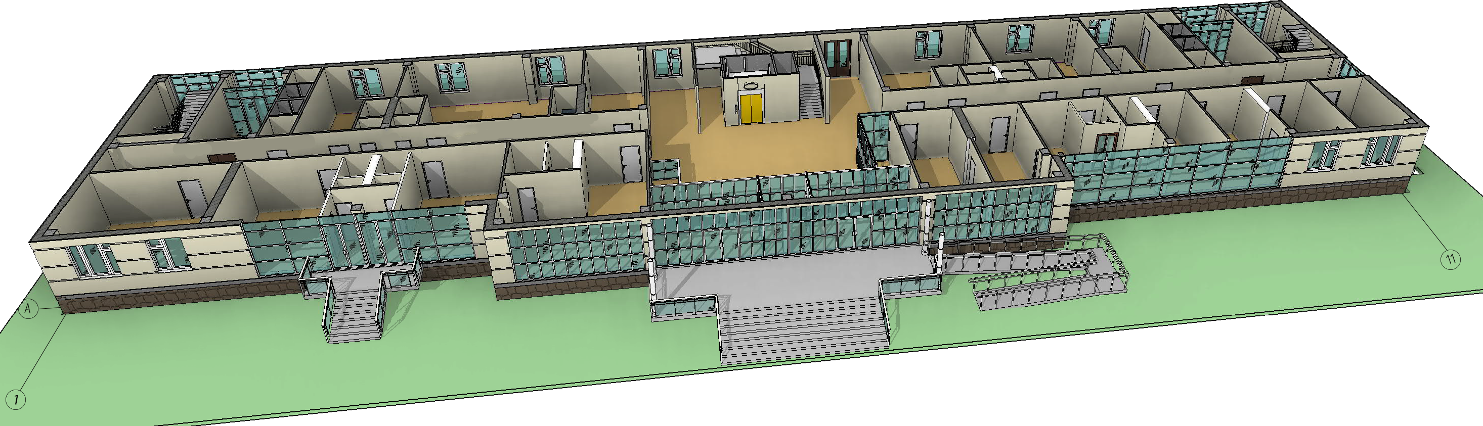
Листы А1/11111111111111113.png
