AliakseiHryhoryeu/graduate-work-construction-engineer/Листы А1/x+.png

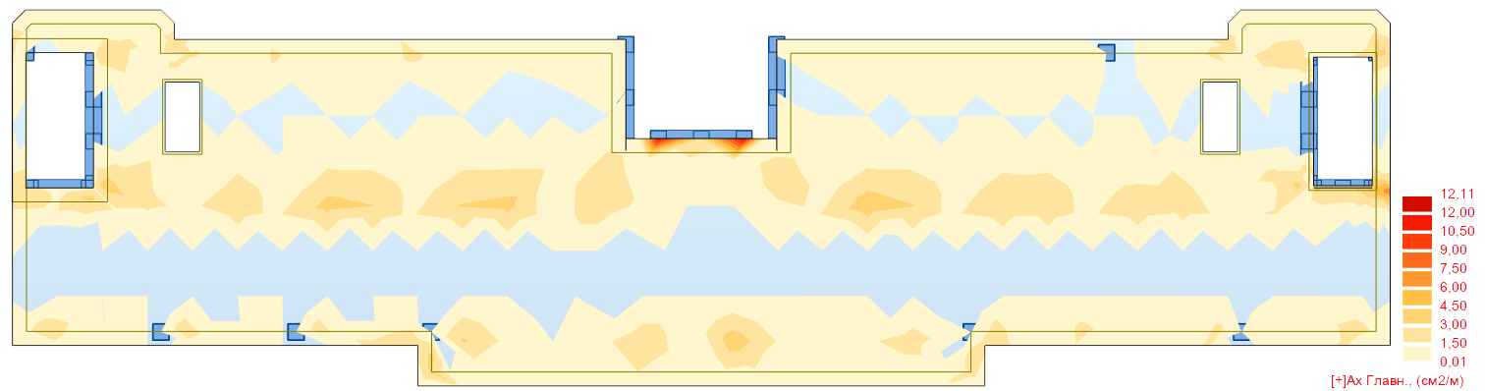
Листы А1/x+.png
