AliakseiHryhoryeu/graduate-work-construction-engineer/Листы А1/y+.png

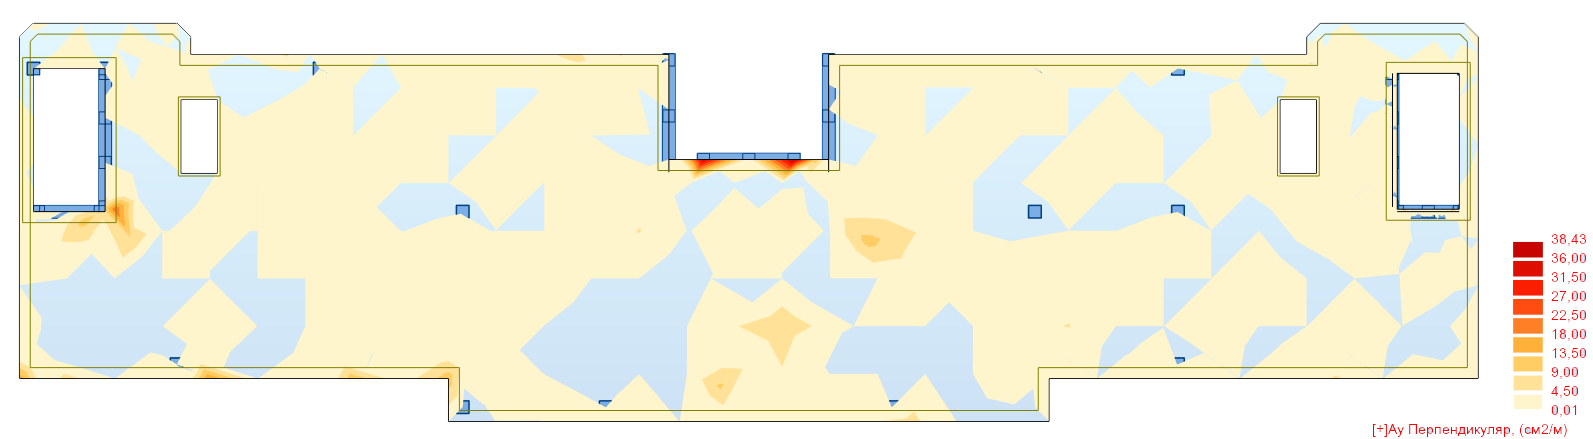
Листы А1/y+.png
