AliakseiHryhoryeu/graduate-work-construction-engineer/Листы А1/Армир верх.png

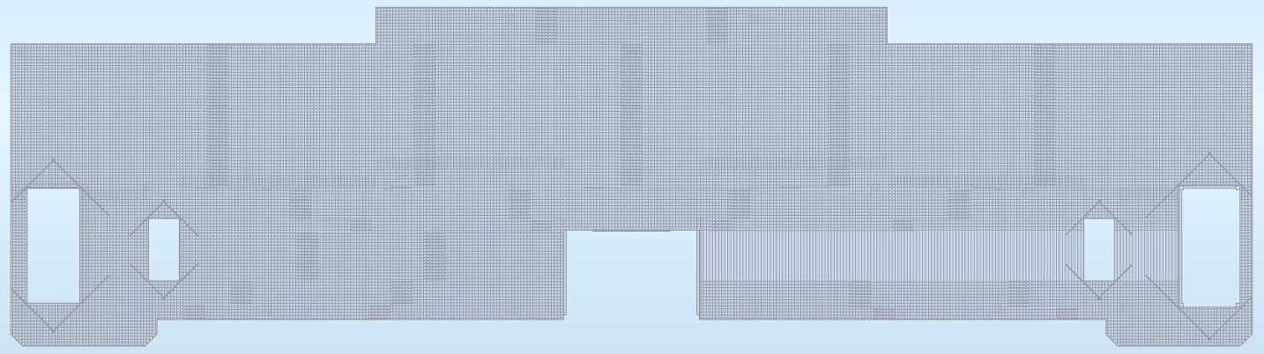
Листы А1/Армир верх.png
