AliakseiHryhoryeu/graduate-work-construction-engineer/Листы А1/Армир низ.png

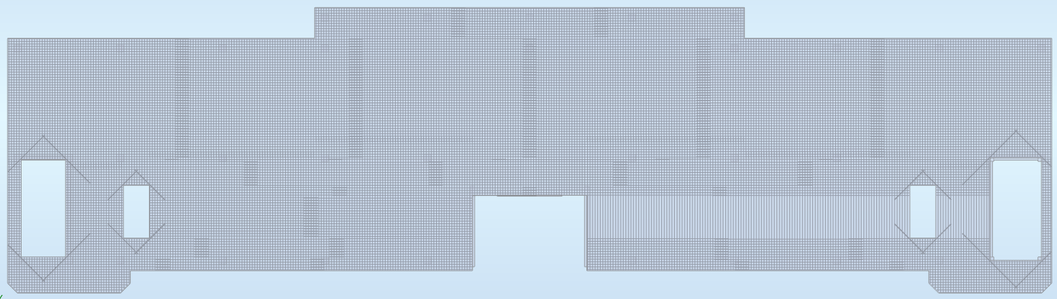
Листы А1/Армир низ.png
