AliakseiHryhoryeu/graduate-work-construction-engineer/Листы А1/демонтаж опалубки.png

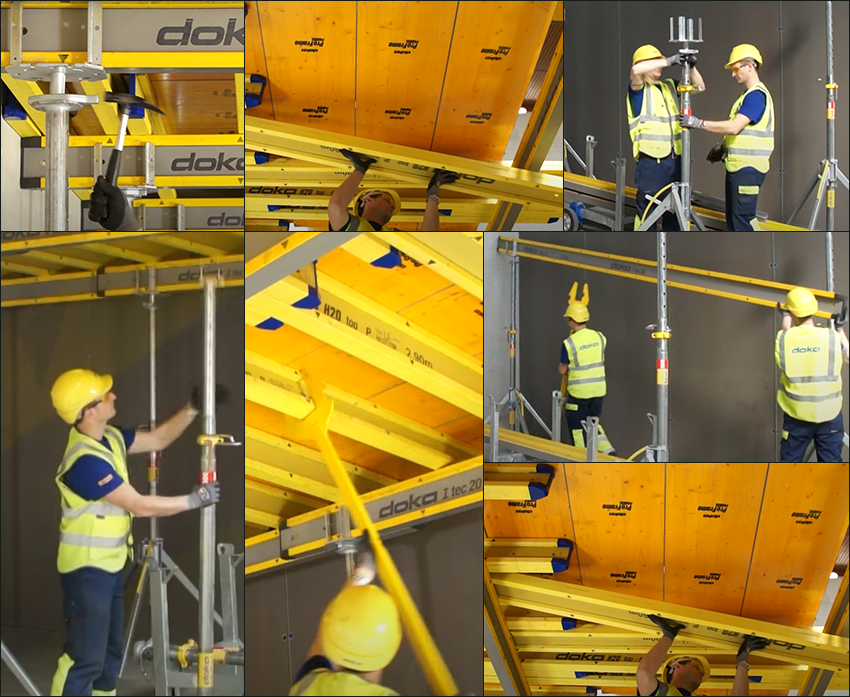
Листы А1/демонтаж опалубки.png
