AliakseiHryhoryeu/graduate-work-construction-engineer/Листы А1/загрузка бадьи1.png

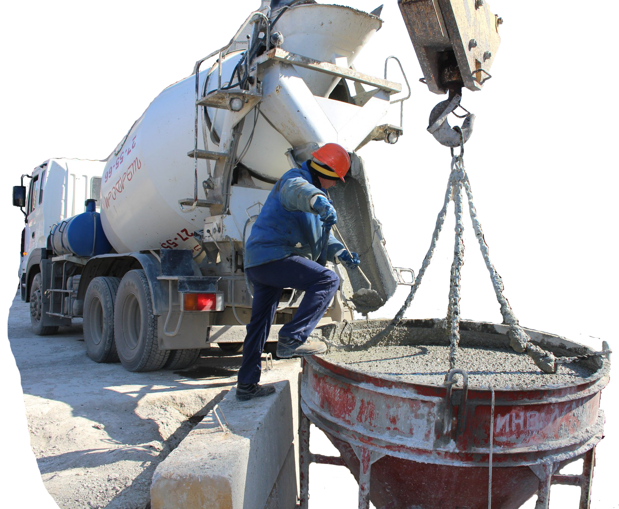
Листы А1/загрузка бадьи1.png
