AliakseiHryhoryeu/graduate-work-construction-engineer/Листы А1/Карта перемещений.png

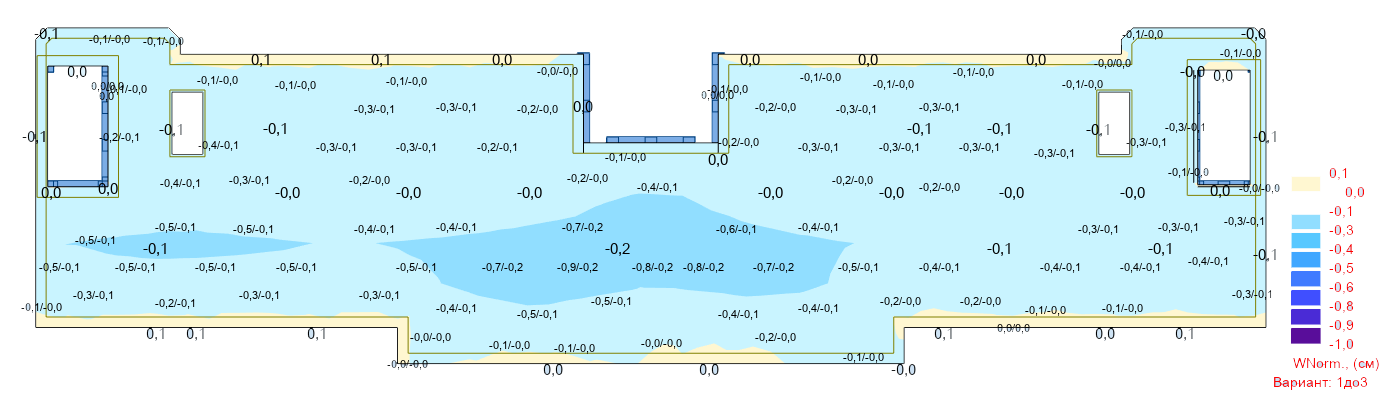
Листы А1/Карта перемещений.png
