AliakseiHryhoryeu/graduate-work-construction-engineer/Листы А1/Пучки арматуры.png

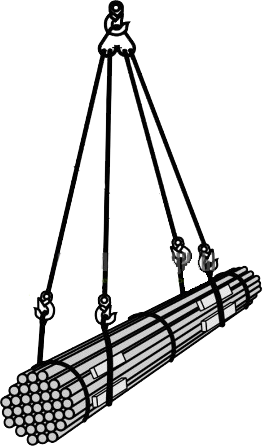
Листы А1/Пучки арматуры.png
