AliakseiHryhoryeu/graduate-work-construction-engineer/Листы А1/разгрузка-бадьи2.png

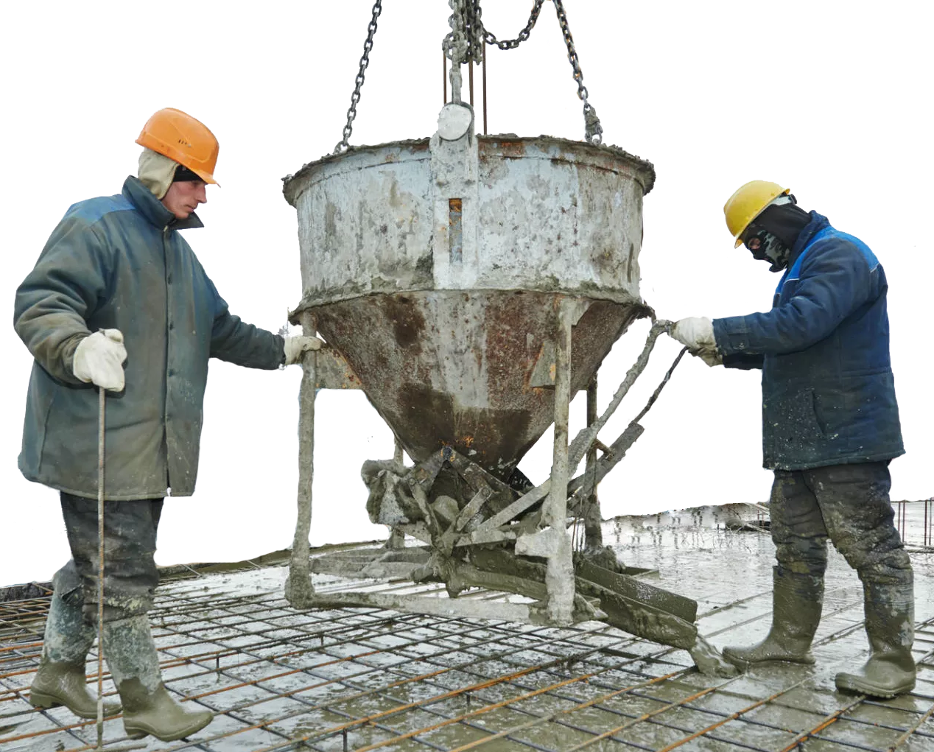
Листы А1/разгрузка-бадьи2.png
