AliakseiHryhoryeu/graduate-work-construction-engineer/Листы А1/Схема армирования плиты перекрытия.jpg

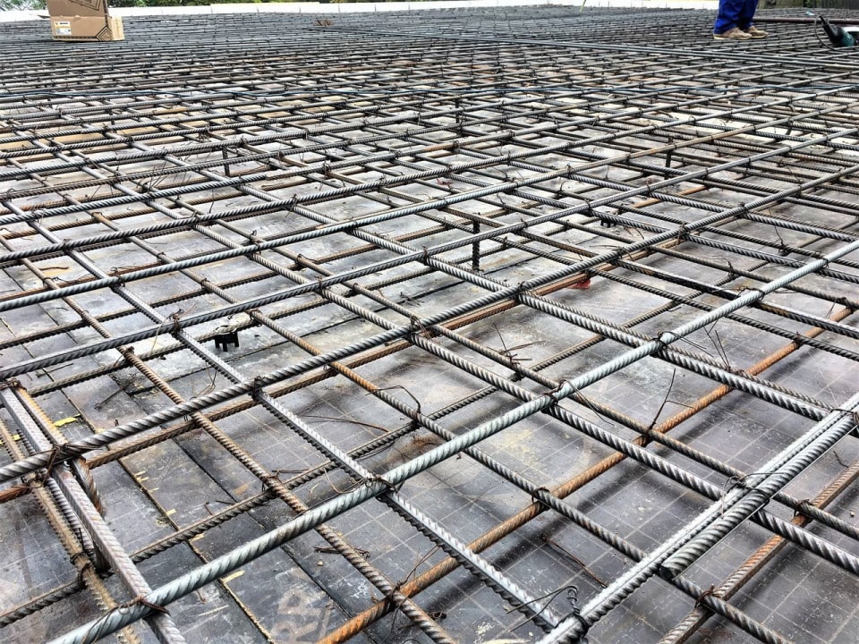
Листы А1/Схема армирования плиты перекрытия.jpg
