AliakseiHryhoryeu/graduate-work-construction-engineer/Листы А1/Схема связки арматуры111.png

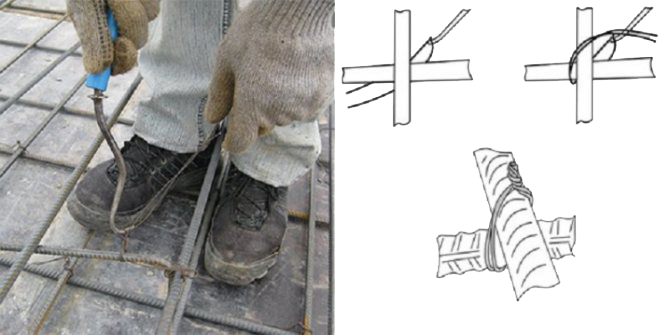
Листы А1/Схема связки арматуры111.png
