AliakseiHryhoryeu/graduate-work-construction-engineer/Листы А1/Схема складирования арматуры.png

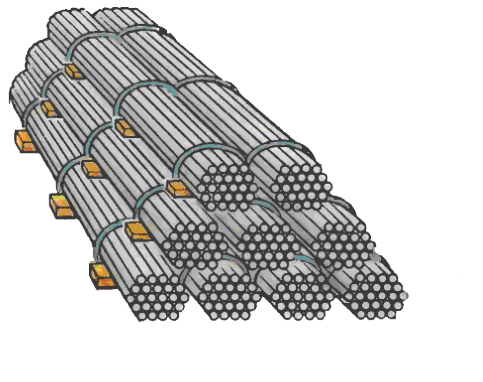
Листы А1/Схема складирования арматуры.png
