AliakseiHryhoryeu/graduate-work-construction-engineer/Листы А1/Схема строповки опалубочных щитов.png

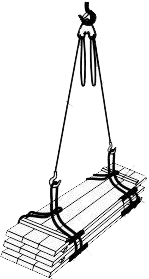
Листы А1/Схема строповки опалубочных щитов.png
