AliakseiHryhoryeu/graduate-work-construction-engineer/Листы А1/телескопическая стойка.png

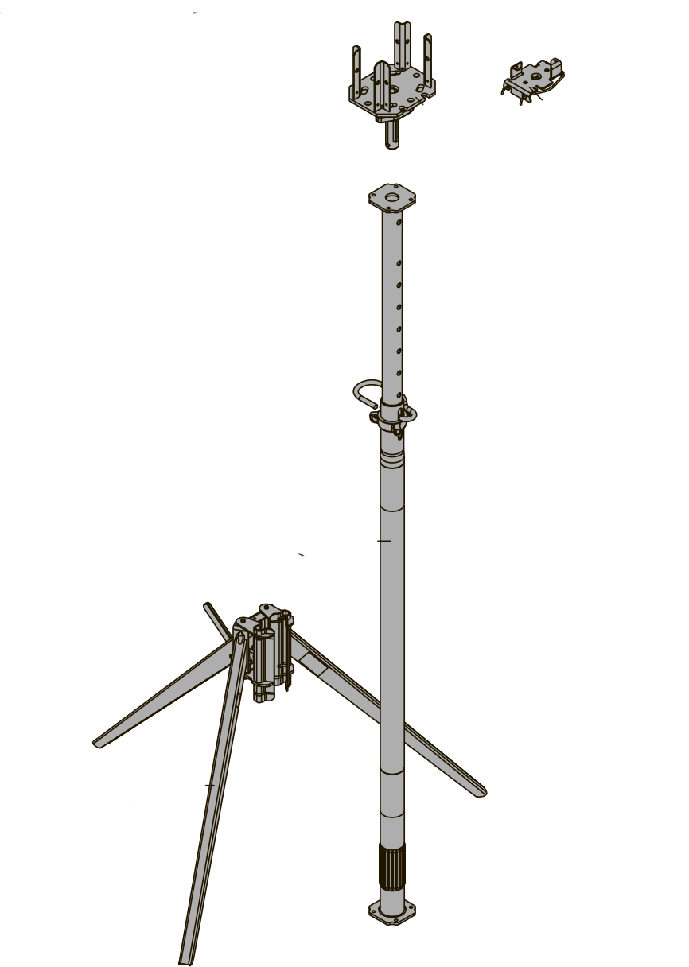
Листы А1/телескопическая стойка.png
