AliakseiHryhoryeu/graduate-work-construction-engineer/Листы А1/уплотнение бетонной смеси.png

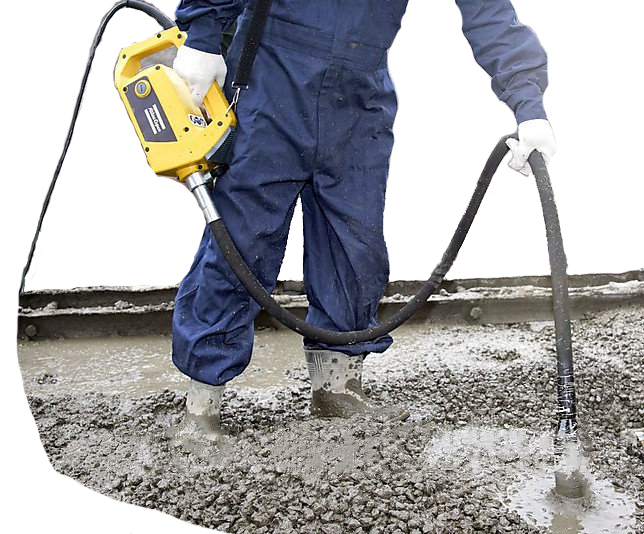
Листы А1/уплотнение бетонной смеси.png
