AliakseiHryhoryeu/graduate-work-construction-engineer/Листы А1/Устройство опалубки.png

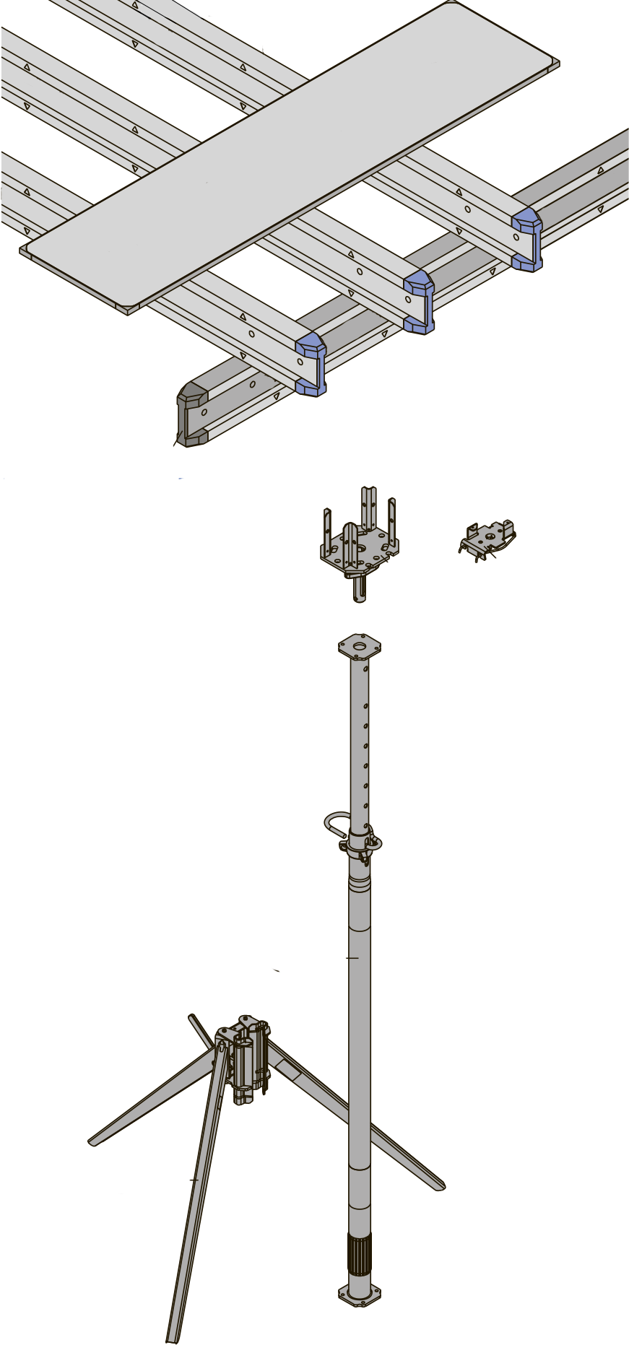
Листы А1/Устройство опалубки.png
