AliakseiHryhoryeu/graduate-work-construction-engineer/4. Организация/Пример диплома/супер всё.xlsx

№ | Обоз-начение | Наименование работ и процессов | Ед. изм. | Объём работ | Состав звена |  |  | Норма вр, чел./маш.-ч. | Трудоемкость, чел./маш.-ч. | Кол-во смен | Прод.работы, дни
 |  |  |  |  | проф. | разр. | кол-во
Нулевой цикл
1 | Е2-1-5 | Срезка растительного слоя бульдозером Т100 ДЗ-8 | 1000 м2 | 0.87 | Машинист | 6 | 1 | 0.84 | 0.731 | 1 | 1
2 | Е2-1-11 | Разработка грунта в отвал | 100м3 | 0.51 | Машинист | 6 | 1 | 3.7 | 1.887 | 1 | 1
3 | Е1-16-2 | Разработка грунта с погрузкой в транспорт | 100м3 | 0.51 | Машинист | 6 | 1 | 4.1 | 2.091 | 1 | 1
4 | E 2-1-31 | Уплотнение грунта самоходным катком | 100м3 | 0.26 | Машинист | 6 | 1 | 0.63 | 0.1638 | 1 | 1
5 | НЗТ,сборник 4.1 шифр 4-328 | Установка деревянной и деревоме-таллической опалубки | 100м2 | 0.925 | Плотник | 4 | 1 | 60.8 | 56.24 | 1 | 3.515
 |  |  |  |  |  | 2 | 1
6 | 6-1-1 | Устройство бетонной подготовки | 100м3 | 0.5 | Бетонщик | 2 | 1 | 95.75 | 47.875 | 1 | 2.9921875
7 | НЗТ,сборник 4.1 шифр 4-513 | Установка сеток и каркасов вручную массой до 50кг | 100 сеток | 1.75 | Арматурщик | 3 | 1 | 23.7 | 41.48 | 1 | 2.5921875
 |  |  |  |  |  | 2 | 1
8 | НЗТ,сборник 4.1 шифр 4-648 | Подача бетонной смеси к месту укладки | 100м3 | 0.266 | Машинист | 4 | 1 | 27 | 7.182 | 1 | 0.89775
 |  |  |  |  | Бетонщик | 2 | 1
9 | НЗТ,сборник 4.1 шифр 4-652 | Укладка бетонной смеси в конструкции обьемом до 3 м3 | 10м3 | 2.66 | Бетонщик | 4 | 1 | 4.1 | 10.906 | 1 | 0.681625
 |  |  |  |  |  | 2 | 1
10 | НЗТ,сборник 4.1 шифр 4-332 | Разборка деревянной и деревоме-таллической опалубки | 100м2 | 0.925 | Плотник | 3 | 1 | 14.9 | 13.783 | 1 | 0.86140625
 |  |  |  |  |  | 2 | 1
11 | НЗТ,сборник 11 шифр 11-455 | Обработка окрасочной гидроизоляцией фундаментов вручную | 100м2 | 0.29 | Гидроизолировщик | 4 | 1 | 4.8 | 1.392 | 1 | 1
 |  |  |  |  |  | 2 | 1
12 | НЗТ,сборник 11 шифр 11-505 | Обработка оклеечной гидроизоляцией фундаментных балок, вручную | 100м2 | 0.29 | Гидроизолировщик | 4 | 1 | 19 | 5.51 | 1 | 1
 |  |  |  |  |  | 3 | 1
 |  |  |  |  |  | 2 | 1
13 | Е2-1-58 | Засыпка грунтом траншей, пазух котлованов и ям с трамбованием до 0,2м | 1м3 | 25 | Землекоп | 2 | 1 | 0.86 | 21.5 | 1 | 1.34375
 |  |  |  |  |  | 1 | 1
Возведение надземной части
14 | НЗТ-4-484 | Установка арматурных сеток и каркасов до 300 кг вертикальных | шт. | 151 | Монтажник | 6 | 1 | 3.5 | 528.5 | 2 | 6.60625
 |  |  |  |  |  | 4 | 2
 |  |  |  |  |  | 3 | 2
 |  |  |  |  | Машинист крана | 6 | 1 | 0.7 | 105.7
15 | НЗТ-4-340 | Монтаж опалубки монолитных колонн периметром свыше 1200мм | шт. | 151 | Монтажник | 6 | 1 | 2.1 | 317.1 | 2 | 3.96375
 |  |  |  |  |  | 4 | 2
 |  |  |  |  |  | 3 | 2
 |  |  |  |  | Машинист крана | 6 | 1 | 0.42 | 63.42 | 2 | 3.96375
16 | НЗТ-4-367 | Монтаж опалубки перекрытий свыше 10м2 | 100 м2 | 27.4 | Плотник | 4 | 1 | 4.1 | 112.34 | 2 | 3.510625
 |  |  |  |  | Плотник | 2 | 1
17 | НЗТ-4-479 | Установка арматурных сеток и каркасов до 300 кг горизонтальных | 100 шт | 1.05 | Арматурщик | 4 | 1 | 0.74 | 0.8 | 1 | 1
 |  |  |  |  |  | 3 | 1
18 | НЗТ-4-652 | Укладка бетонной смеси в опалубку колонн периметром свыше 1200 метров краном в бадьях объемом до 3м3 | 10м3 | 68.5 | бетонщик | 4 | 1 | 1.9 | 130.2 | 2 | 2.03359375
 |  |  |  |  |  | 2 | 1
 |  |  |  |  | Машинист | 6 | 1 | 0.5 | 34.25
19 | НЗТ-4-652 | Укладка бетонной смеси в опалубку перекрытий площадью свыше 10 м2 метров краном в бадьях объемом до 3м3 | 100м3 | 2.4 | Бетонщик | 4 | 1 | 130 | 312 | 1 | 9.75
 |  |  |  |  |  | 2 | 1
 |  |  |  |  | Машинист | 6 | 1
20 | НЗТ,сборник 5.1 шифр 5-205 | Демонтаж опалубки перекрытий свыше 10м2 | 100м2 | 27.4 | Плотник | 4 | 1 | 9.1 | 249.34 | 1 | 6.2335
 |  |  |  |  |  | 2 | 1
21 | НЗТ-4-195 | Монтаж лифтовых шахттолщиной до 200мм | 10шт | 0.5 | монтажник | 5 | 1 | 0.36 | 0.18 | 1 | 1
 |  |  |  |  |  | 4 | 1
 |  |  |  |  |  | 3 | 2
 |  |  |  |  | машинист | 6 | 1 |  |  |  |  |  |  |  | 298.12 | 6.21085
22 | НЗТ,сборник 19 шифр19-226 | Кладка наружных стен из газосиликатных блоков на клею | 100м3 | 15.100 | кам-щик | 5 | 4 | 22.5 | 339.75 | 1 | 10.6171875
 |  |  |  |  |  | 4 | 4
 |  |  |  |  |  | 3 | 12
23 | НЗТ,сборник 5.1 шифр 5-205 | Кладка перегородок из газосиликатных блоков | 100м3 | 0.74 | кам-щик | 4 | 5 | 9.1 | 6.734 | 1 | 2
 |  |  |  |  |  | 2 | 5
24 | Е7-44-10 | Устройство перемычек | 100шт. | 1.84 | кам-щик | 2 | 3 | 0.35 | 0.644 | 1 | 1
25 | НЗТ сборник №7, шифр 7- 131 | Устройство пароизоляции под кровлю рулонными материалами | 100м2 | 5.480 | Изолировщик | 3 | 2 | 6.70 | 36.72 | 1 | 1
 |  |  |  |  |  | 2 | 2
26 | НЗТ сборник №7, шифр 7- 148 | Устройство теплоизоляции(укладка минеральной ваты толщиной до 200мм) | 100м2 | 5.480 | Изолировщик | 3 | 2 | 5.0 | 27.40 | 2 | 1.7125
 |  |  |  |  |  | 2 | 2
27 | НЗТ сборник №7, шифр 7-157 | Устройство стяжки | 100м2 | 5.480 | Изолировщик | 3 | 1 | 13.5 | 73.98 | 2 | 2.311875
 |  |  |  |  |  | 2 | 1
28 | НЗТ сборник №7, шифр 7-16 | Очистка основания от мусора механизированным способом | 100м2 | 5.480 | Кровельщик | 3 | 1 | 0.41 | 2.25 | 1 | 1
 |  |  |  |  |  | 2 | 1
29 | НЗТ сборник №7, шифр 7-17 | Просушивание влажных мест ос-нования механизи-рованным способом (20%) | 100м2 | 5.480 | Кровельщик | 4 | 3 | 8.60 | 47.13 | 1 | 2
30 | НЗТ сборник №7, шифр 7-19 | Огрунтовка поверхности основания битумной мастикой механизированным способом | 100м2 | 5.480 | Кровельщик | 4 | 1 | 0.65 | 3.56 | 1 | 1
31 | НЗТ сборник №7, шифр 7-7 | Покрытие крыш наплавляемым материалом ТЕХНОНИКОЛЬ | 100м2 | 21.92 | Кровельщик | 4 | 1 | 4.6 | 100.83 | 1 | 6.302
 |  |  |  |  |  | 3 | 1
32 | НЗТ сборник №7, шифр 7-22 | Обделка водосточных воронок | 1 воронка | 4 | Кровельщик | 5 | 1 | 1.3 | 5.2 | 1 | 1
33 | НЗТ сборник №7, шифр 7-25 | Обделка свесов и примыканий рулонными материалами | 100м2 | 0.24 | Кровельщик | 4 | 1 | 4.4 | 1.06 | 1 | 1
 |  |  |  |  |  | 3 | 1
34 | НЗТ сборник №6, шифр 6-653 | Установка оконных блоков с тройным остеклением площадью до 2 м2 | 100м2 | 0.970 | Плотник | 4 | 1 | 101.7 | 98.65 | 1 | 6.1655625
 |  |  |  |  |  | 2 | 1
35 | НЗТ сборник №6, шифр 6-175 | Установка дверных блоков площадью до 2,5м2 | 100м2 | 0.446 | Плотник | 4 | 1 | 16 | 7.14 | 1 | 2
 |  |  |  |  |  | 2 | 1
36 | НЗТ сборник №6, шифр 6-185 | Установка дверных блоков площадью 4 м2 и более | 100м2 | 0.113 | Плотник | 4 | 1 | 13.4 | 1.52 | 1 | 2
 |  |  |  |  |  | 2 | 1
Отделочные работы
Стены
37 | НЗТ сборник №8.1, шифр 8-51 | Простое оштукатуривание вручную (обрызг) | 100м2 | 19.14 | Штукатур | 3 | 4 | 35.8 | 685.21 | 2 | 30
38 | НЗТ сборник №8.1, шифр 8-1263 | Грунтовка поверхности составом "варио путс" валиком | 100м2 | 18.230 | Штукатур | 5 | 1 | 8.2 | 149.49 | 2 | 4
 |  |  |  |  |  | 4 | 1
39 | НЗТ сборник №8.1, шифр 8-1265 | Нанесение покрытия "варио путс" пистолетом-распылителем за 2 раза | 100м2 | 18.230 | Штукатур | 5 | 1 | 14.2 | 258.9 | 2 | 13
 |  |  |  |  |  | 4 | 3
40 | НЗТ сборник №8.1, шифр 8-1267 | Приготовление штукатурной массы путем перемешивания миксером | 100 кг | 50.080 | Штукатур | 4 | 1 | 0.59 | 29.55 | 1 | 1.8467
41 | НЗТ сборник №8.1, шифр 8-1186 | Облицовка внутренних поверхностей плиткой 150*150мм | 100м2 | 0.91 | Облицовщик-плиточник | 5 | 2 | 139 | 126.49 | 1 | 3
 |  |  |  |  |  | 4 | 2
Полы
42 | НЗТ сборник №19, шифр 19-262 | Устройство полов из ламинированных панелей по бетонному основанию | 100м2 | 20.2 | Столяр | 4 | 2 | 48.4 | 977.68 | 2 | 15.27625
 |  |  |  |  |  | 3 | 2
43 | НЗТ сборник №19, шифр 19-111 | Устройство полов из керамогранита | 100м2 | 1.13 | Облицовщик-плиточник | 4 | 2 | 52.4 | 59.21 | 2 | 1.850375
44 | НЗТ сборник №19, шифр 19-35 | Устройство паркетных полов | 100м2 | 47 | Облицовщиксинтетическими материалами | 4 | 1 | 7.8 | 366.60 | 2 | 11.45625
 |  |  |  |  |  | 3 | 1
 |  |  |  |  |  | 2 | 1
45 | НЗТ сборник №19, шифр 19-111 | Устройство полов из керамических плиток 200*200 мм | 100м2 | 1.28 | Облицовщик-плиточник | 4 | 2 | 55 | 70.4 | 1 | 4
 |  |  |  |  |  | 3 | 2
Потолки
46 | НЗТ сборник №8.3, шифр 8-1923 | Разметка потолков | 100м2 | 2.790 | Монтажники конструкций | 5 | 2 | 10 | 27.9 | 1 | 3
 |  |  |  |  |  | 4 | 2
47 | НЗТ сборник №8.3, шифр 8-1923 | Монтаж металлических конструкций караса | 100м профиля | 2.02 | Монтажники конструкций | 4 | 2 | 4.2 | 8.48 | 1 | 4
48 | НЗТ сборник №8.3, шифр 8-1942 | Облицовка потолков алюминиевыми плитами по готовому каркасу | 100м2 | 2.020 | Монтажники конструкций | 4 | 2 | 35.9 | 72.52 | 1 | 10 |  |  |  |  |  | Наименование работ и процессов | % от трудоемкости общестрои-тельных работ | Трудо-емкость, чел.-час. | Количество | Продолжительность
 |  |  |  |  |  | 3 | 2
Наружные работы
49 | Е15-372-1 | Устройтво вентилируемых фасадов | 100м2 | 16.84 | Монтажник конструкций | 4 | 4 | 234.46 | 3948.3064 | 2 | 41.13
 |  |  |  |  |  | 3 | 2 |  |  |  |  |  |  |  |  |  | 1 | 2 | 3 | 4 | 5
51 | Е31-18-1 | Устройство асфальтовой отмостки на щебеночном основании толщиной 200мм | 100м2 | 0.765 | Асфальтировщик | 4 | 1 | 38.15 | 29.18 | 1 | 1.21603125 |  |  |  |  |  | Ввод коммуникаций | 2 | 193.71 | 4 | 4.00
 |  |  |  |  |  | 3 | 1 |  |  |  |  |  |  |  |  |  | Внутренние сантехнические работы | 10 | 968.54 | 10 | 12.00
 |  |  |  |  |  | 2 | 1 |  |  |  |  |  |  |  |  |  | Электротехнические работы | 8 | 774.83 | 8 | 12.00
52 | Е8-27-1 | Устройство крылец с входной площадкой | м2 | 30.44 | Бетонщик | 4 | 1 | 1.92 | 58.44 | 1 | 3.6528 |  |  |  |  |  | Благоустройство территории | 4 | 387.42 | 5 | 9.00
 |  |  |  |  |  | 2 | 1 |  |  |  |  |  |  |  |  |  | Прочие работы | 5 | 484.27 | 5 | 12.00
Итого |  |  |  |  |  |  |  |  | #REF!
 |  |  |  |  |  |  |  |  | 9685.377 |  |  |  |  |  |  |  |  | #REF!
 |  |  |  |  |  |  |  |  | 9685
 |  |  |  |  |  |  |  |  |  |  |  |  |  |  |  |  | 12493.76 | 12493.76
 |  |  |  | № | Обоз-начение | Наименование работ и процессов | Ед. изм. | Объём работ | Состав звена |  |  | Норма вр, чел./маш.-ч. | Трудоемкость, чел./маш.-ч. | Кол-во смен | Прод.работы, дни
 |  |  |  |  |  |  |  |  | проф. | разр. | кол-во
 |  |  |  | Нулевой цикл
 |  |  |  | 1 | Е2-1-5 | Срезка растительного слоя бульдозером Т100 ДЗ-8 | 1000 м2 | 0.87 | Машинист | 6 | 1 | 0.84 | 0.731 | 1 | 1
 |  |  |  | 2 | Е2-1-11 | Разработка грунта в котлованах одноковшовыми экскаваторами | 100м3 | 0.61 | Машинист | 6 | 1 | 3.5 | 2.135 | 1 | 1
 |  |  |  | 3 | E 2-1-31 | Уплотнение грунта самоходным катком | 100м3 | 0.26 | Машинист | 6 | 1 | 0.63 | 0.1638 | 1 | 1
 |  |  |  | 4 | НЗТ,сборник 4.1 шифр 4-328 | Установка деревянной и деревоме-таллической опалубки | 100м2 | 0.925 | Плотник | 4 | 1 | 60.8 | 56.24 | 1 | 4
 |  |  |  |  |  |  |  |  |  | 2 | 1
 |  |  |  | 5 | 6-1-1 | Устройство бетонной подготовки | 100м3 | 0.5 | Бетонщик | 2 | 1 | 95.75 | 47.875 | 1 | 3
 |  |  |  | 6 | НЗТ,сборник 4.1 шифр 4-513 | Установка сеток и каркасов вручную массой до 50кг | 100 сеток | 1.75 | Арматурщик | 3 | 1 | 23.7 | 41.48 | 1 | 3
 |  |  |  |  |  |  |  |  |  | 2 | 1
 |  |  |  | 7 | НЗТ,сборник 4.1 шифр 4-648 | Подача бетонной смеси к месту укладки | 100м3 | 0.266 | Машинист | 4 | 1 | 27 | 7.182 | 1 | 1
 |  |  |  |  |  |  |  |  | Бетонщик | 2 | 1
 |  |  |  | 8 | НЗТ,сборник 4.1 шифр 4-652 | Укладка бетонной смеси в конструкции обьемом до 3 м3 | 10м3 | 2.66 | Бетонщик | 4 | 1 | 4.1 | 10.906 | 1 | 1
 |  |  |  |  |  |  |  |  |  | 2 | 1
 |  |  |  | 9 | НЗТ,сборник 4.1 шифр 4-332 | Разборка деревянной и деревоме-таллической опалубки | 100м2 | 0.925 | Плотник | 3 | 1 | 14.9 | 13.783 | 1 | 1
 |  |  |  |  |  |  |  |  |  | 2 | 1
 |  |  |  | 10 | НЗТ,сборник 11 шифр 11-455 | Обработка окрасочной гидроизоляцией фундаментов вручную | 100м2 | 0.29 | Гидроизолировщик | 4 | 1 | 4.8 | 1.392 | 1 | 1
 |  |  |  |  |  |  |  |  |  | 2 | 1
 |  |  |  | 11 | НЗТ,сборник 11 шифр 11-505 | Обработка оклеечной гидроизоляцией фундаментных балок, вручную | 100м2 | 0.29 | Гидроизолировщик | 4 | 1 | 19 | 5.51 | 1 | 1
 |  |  |  |  |  |  |  |  |  | 3 | 1
 |  |  |  |  |  |  |  |  |  | 2 | 1
 |  |  |  | 12 | Е2-1-58 | Засыпка грунтом траншей, пазух котлованов и ям с трамбованием до 0,2м | 1м3 | 25 | Землекоп | 2 | 1 | 0.86 | 21.5 | 1 | 1
 |  |  |  |  |  |  |  |  |  | 1 | 1
 |  |  |  | Возведение надземной части
 |  |  |  | 13 | НЗТ-4-484 | Установка арматурных сеток и каркасов до 300 кг вертикальных | шт. | 151 | Монтажник | 6 | 1 | 3.5 | 528.5 | 2 | 7
 |  |  |  |  |  |  |  |  |  | 4 | 2
 |  |  |  |  |  |  |  |  |  | 3 | 2
 |  |  |  |  |  |  |  |  | Машинист крана | 6 | 1 | 0.7 | 105.7
 |  |  |  | 14 | НЗТ-4-340 | Монтаж опалубки монолитных колонн периметром свыше 1200мм | шт. | 151 | Монтажник | 6 | 1 | 2.1 | 317.1 | 2 | 4
 |  |  |  |  |  |  |  |  |  | 4 | 2
 |  |  |  |  |  |  |  |  |  | 3 | 2
 |  |  |  |  |  |  |  |  | Машинист крана | 6 | 1 | 0.42 | 63.42 | 2 | 4
 |  |  |  | 15 | НЗТ-4-367 | Монтаж опалубки перекрытий свыше 10м2 | 100 | 27.4 | Плотник | 4 | 1 | 4.1 | 112.34 | 2 | 4
 |  |  |  |  |  |  | м2
 |  |  |  |  |  |  |  |  | Плотник | 2 | 1
 |  |  |  | 15 | НЗТ-4-479 | Установка арматурных сеток и каркасов до 300 кг горизонтальных | 100 шт | 1 | Арматурщик | 4 | 1 | 0.74 | 0.8 | 1 | 1
 |  |  |  |  |  |  |  |  |  | 3 | 1
 |  |  |  | 17 | НЗТ-4-652 | Укладка бетонной смеси в опалубку колонн периметром свыше 1200 метров краном в бадьях объемом до 3м3 | 10м3 | 68.5 | бетонщик | 4 | 1 | 1.9 | 130.2 | 2 | 2
 |  |  |  |  |  |  |  |  |  | 2 | 1
 |  |  |  |  |  |  |  |  | Машинист | 6 | 1 | 0.5 | 34
 |  |  |  | 18 | НЗТ-4-652 | Укладка бетонной смеси в опалубку перекрытий площадью свыше 10 м2 метров краном в бадьях объемом до 3м3 | 100м3 | 2.4 | Бетонщик | 4 | 1 | 312 | 48.1 | 1 | 10
 |  |  |  |  |  |  |  |  |  | 2 | 1
 |  |  |  |  |  |  |  |  | Машинист | 6 | 1
 |  |  |  | 19 | НЗТ,сборник 5.1 шифр 5-205 | Демонтаж опалубки перекрытий свыше 10м2 | 100м2 | 27.4 | Плотник | 4 | 1 | 9.1 | 249.34 | 1 | 6
 |  |  |  |  |  |  |  |  |  | 2 | 1
 |  |  |  |  | НЗТ-4-195 | Монтаж лифтовых шахттолщиной до 200мм | 10шт | 0.5 | монтажник | 5 | 1 | 0.36 | 0.18 | 1 | 1
 |  |  |  | 20
 |  |  |  |  |  |  |  |  |  | 4 | 1
 |  |  |  |  |  |  |  |  |  | 3 | 2
 |  |  |  |  |  |  |  |  | машинист | 6 | 1
 |  |  |  | 21 | НЗТ,сборник 19 шифр19-226 | Кладка наружных стен из газосиликатных блоков на клею | 100м3 | 15.1 | кам-щик | 5 | 4 | 22.5 | 339.75 | 1 | 11
 |  |  |  |  |  |  |  |  |  | 4 | 4
 |  |  |  |  |  |  |  |  |  | 3 | 12
 |  |  |  | 22 | НЗТ,сборник 5.1 шифр 5-205 | Кладка перегородок из газосиликатных блоков | 100м3 | 0.74 | кам-щик | 4 | 5 | 9.1 | 7 | 1 | 2
 |  |  |  |  |  |  |  |  |  | 2 | 5
 |  |  |  | 23 | НЗТ сборник №7, шифр 7- 131 | Устройство пароизоляции под кровлю рулонными материалами | 100м2 | 5.48 | Изолировщик | 3 | 1 | 6.7 | 36.72 | 2 | 1
 |  |  |  |  |  |  |  |  |  | 2 | 1
 |  |  |  | 24 | НЗТ сборник №7, шифр 7- 148 | Устройство теплоизоляции(укладка минеральной ваты толщиной до 200мм) | 100м2 | 5.48 | Изолировщик | 3 | 1 | 5 | 27.4 | 2 | 1
 |  |  |  |  |  |  |  |  |  | 2 | 2
 |  |  |  | 25 | НЗТ сборник №7, шифр 7-157 | Устройство стяжки | 100м2 | 5.48 | Изолировщик | 3 | 1 | 13.5 | 73.98 | 2 | 2
 |  |  |  |  |  |  |  |  |  | 2 | 1
 |  |  |  | 26 | НЗТ сборник №7, шифр 7-16 | Очистка основания от мусора механизированным способом | 100м2 | 5.48 | Кровельщик | 3 | 1 | 0.41 | 2.25 | 1 | 1
 |  |  |  |  |  |  |  |  |  | 2 | 1
 |  |  |  | 27 | НЗТ сборник №7, шифр 7-17 | Просушивание влажных мест ос-нования механизи-рованным способом | 100м2 | 5.48 | Кровельщик | 4 | 2 | 8.6 | 47.13 | 2 | 3
 |  |  |  |  |  | -20%
 |  |  |  | 28 | НЗТ сборник №7, шифр 7-19 | Огрунтовка поверхности основания битумной мастикой | 100м2 | 5.48 | Кровельщик | 4 | 1 | 0.65 | 3.56 | 1
 |  |  |  |  |  |  |  |  |  |  |  |  |  |  | 1
 |  |  |  | 29 | НЗТ сборник №7, шифр 7-7 | Покрытие крыш наплавляемым рубероидом с оплавлением покровного слоя | 100м2 | 21.92 | Кровельщик | 4 | 1 | 4.6 | 100.83 | 1 | 3
 |  |  |  |  |  |  |  |  |  | 3 | 2
 |  |  |  | 30 | НЗТ сборник №7, шифр 7-22 | Обделка водосточных воронок | 1 воронка | 4 | Кровельщик | 5 | 1 | 1.3 | 5.2 | 1 | 1
 |  |  |  | 31 | НЗТ сборник №7, шифр 7-25 | Обделка свесов и примыканий рулонными материалами | 100м2 | 0.24 | Кровельщик | 4 | 1 | 4.4 | 1.06 | 1 | 1
 |  |  |  |  |  |  |  |  |  | 3 | 1
 |  |  |  | 32 | НЗТ сборник №8.1, шифр 8-1294 | Остекление витражей с каркасом из алюминиевого профиля стеклопакетами площадью до 3 м2 внутри помещения | 100м2 | 0.68 | Стекольщик | 5 | 2 | 130 | 88.4 | 1 | 3
 |  |  |  |  |  |  |  |  |  | 4 | 2
 |  |  |  | 33 | НЗТ сборник №6, шифр 6-653 | Установка оконных блоков с тройным остеклением площадью до 2 м2 | 100м2 | 0.97 | Плотник | 4 | 2 | 101.7 | 98.65 | 1 | 3
 |  |  |  |  |  |  |  |  |  | 2 | 2
 |  |  |  | 34 | НЗТ сборник №6, шифр 6-175 | Установка дверных блоков площадью до 2,5м2 | 100м2 | 0.446 | Плотник | 4 | 2 | 16 | 7.14 | 1 | 1
 |  |  |  |  |  |  |  |  |  | 2 | 2
 |  |  |  | 35 | НЗТ сборник №6, шифр 6-185 | Установка дверных блоков площадью 4 м2 и более | 100м2 | 0.113 | Плотник | 4 | 2 | 13.4 | 1.52 | 1 | 1
 |  |  |  |  |  |  |  |  |  | 2 | 2
 |  |  |  | Отделочные работы
 |  |  |  | Стены
 |  |  |  | 36 | НЗТ сборник №8.1, шифр 8-51 | Простое оштукатуривание вручную (обрызг) | 100м2 | 19.14 | Штукатур | 3 | 3 | 10.3 | 197.14 | 1 | 5
 |  |  |  | 37 | НЗТ сборник №8.1, шифр 8-1263 | Грунтовка поверхности составом "варио путс" валиком | 100м2 | 18.23 | Штукатур | 5 | 2 | 8.2 | 149.49 | 1 | 5
 |  |  |  |  |  |  |  |  |  | 4 | 2
 |  |  |  | 38 | НЗТ сборник №8.1, шифр 8-1265 | Нанесение покрытия "варио путс" пистолетом-распылителем за 2 раза | 100м2 | 18.23 | Штукатур | 5 | 1 | 14.2 | 258.9 | 1 | 15
 |  |  |  |  |  |  |  |  |  | 4 | 1
 |  |  |  | 39 | НЗТ сборник №8.1, шифр 8-1267 | Приготовление штукатурной массы путем перемешивания миксером | 100 кг | 50.08 | Штукатур | 4 | 1 | 0.59 | 29.55 | 1 | 2
 |  |  |  | 40 | НЗТ сборник №8.1, шифр 8-1186 | Облицовка внутренних поверхностей плиткой 150*150мм | 100м2 | 0.91 | Облицовщик-плиточник | 5 | 1 | 139 | 126.49 | 1 | 10
 |  |  |  |  |  |  |  |  |  | 4 | 1
 |  |  |  | Полы
 |  |  |  | 41 | НЗТ сборник №19, шифр 19-262 | Устройство полов из ламинированных панелей по бетонному основанию | 100м2 | 20.2 | Столяр | 4 | 2 | 48.4 | 977.68 | 2 | 15
 |  |  |  |  |  |  |  |  |  | 3 | 2
 |  |  |  | 42 | НЗТ сборник №19, шифр 19-35 | Устройство паркетных полов | 100м2 | 47 | Облицовщиксинтетическими материалами | 4 | 1 | 7.8 | 366.6 | 2 | 11
 |  |  |  |  |  |  |  |  |  | 3 | 1
 |  |  |  |  |  |  |  |  |  | 2 | 1
 |  |  |  | 43 | НЗТ сборник №19, 19-111 | Устройство полов из керамических плиток 200*200 мм | 100м2 | 1.28 | Облицовщик-плиточник | 4 | 1 | 55 | 70.4 | 1 | 5
 |  |  |  |  |  |  |  |  |  | 3 | 1
 |  |  |  | Потолки
 |  |  |  | 44 | НЗТ сборник №8.3, шифр 8-1923 | Разметка потолков | 100м2 | 2.79 | Монтажники конструкций | 5 | 1 | 10 | 27.9 | 1 | 2
 |  |  |  |  |  |  |  |  |  | 4 | 1
 |  |  |  | 45 | НЗТ сборник №8.3, шифр 8-1923 | Монтаж металлических конструкций караса | 100м профиля | 2.02 | Монтажники конструкций | 4 | 1 | 4.2 | 8.48 | 1 | 2
 |  |  |  | 46 | НЗТ сборник №8.3, шифр 8-1942 | Облицовка потолков алюминиевыми плитами по готовому каркасу | 100м2 | 2.02 | Монтажники конструкций | 4 | 1 | 35.9 | 72.52 | 1 | 85
 |  |  |  |  |  |  |  |  |  | 3 | 1
 |  |  |  | Наружные работы
 |  |  |  | 47 | Е15-372-1 | Устройтво вентилируемых фасадов | 100м2 | 16.84 | Монтажник конструкций | 4 | 4 | 234.46 | 3948.3064 | 2 | 41
 |  |  |  |  |  |  |  |  |  | 3 | 2
 |  |  |  | 48 | Е31-18-1 | Устройство асфальтовой отмостки на щебеночном основании толщиной 200мм | 100м2 | 0.765 | Асфальтировщик | 4 | 1 | 38.15 | 29.18 | 1 | 1
 |  |  |  |  |  |  |  |  |  | 3 | 1
 |  |  |  |  |  |  |  |  |  | 2 | 1
 |  |  |  | 49 | Е8-27-1 | Устройство крылец с входной площадкой | м2 | 30.44 | Бетонщик | 4 | 1 | 1.92 | 58.44 | 1 | 4
 |  |  |  |  |  |  |  |  |  | 2 | 1
 |  |  |  | Итого |  |  |  |  |  |  |  |  | 8960.108
