AliakseiHryhoryeu/graduate-work-construction-engineer/5. Экономика/Пример/ekonomika объектный.xlsx

ведомость V работ |  |  |  |  |  |  |  |  |  |  |  |  |  |  | 7.2
срезка раст слоя гр | 4.98 |  |  |  |  |  |  |  | Наименование показателя |  |  | Единица измерения | Формула расчета | Значение показателя |  | Проектируемое здание
планировка | 14.98 |  |  |  |  |  |  |  | 1 |  |  | 2 |  | 3 | Наименование показателей | руб. | В процентах к итогу
разработка гр экскаватором в отвал | 1072.66 | 5.36 |  |  |  |  |  |  | 1. Мощность |  |  |  |  |  | Заработная плата рабочих, руб. | 614094.78 | 24.98
 | 24.37 | 1.71 |  |  |  |  |  |  | 2. Площадь |  |  | га |  | 1.44 | Затраты на эксплуатацию строительных машин и механизмов, руб. | 127725.27 | 5.20
 | 20.13 | 1.79 |  |  |  |  |  |  | 3. Площадь застройки |  |  | м2 |  | 14400 | в том числе заработная плата рабочих, руб. |  | 0.00
 | Vотв | 1.87 |  |  |  |  |  |  | 4. Число этажей |  |  | этаж |  | 1 | Материалы, руб. | 618476.36 | 25.16
 |  | 2.09 |  |  |  |  |  |  | 5. Здание отапливаемое, неотапливаемое |  |  |  |  | отапливаемое | Транспортные затраты, руб. | 80207.68 | 3.26
Разработка грунта экскаватором на вызов | Vвыв | 3.50 |  |  |  |  |  |  | 6. Конструктивный тип (кирпичный, панельный, каркасно-панельный, каркасно-блочный, мобильный (инвентарный) и др.) |  |  |  |  | панельный | Общехозяйственные и общепроизводственные расходы, руб. | 377819.32 | 15.37
Доработка грунта в ручную | 0.53 | 0.59 |  |  |  |  |  |  | 7. Строительный объем, в т.ч. подземной части |  |  | м³ | 96*156*13,3 | 199180.8 | Итого себестоимости СМР, руб. | 1818323.41 | 73.96
Устройство фундаментов сборных | 2.73 |  |  |  |  |  |  |  | 8. Общая площадь |  |  | м² | 96*156 | 14976 | Плановая прибыль, руб. | 416826.70 | 16.95
Подготовка стен под окраску | 5.32 |  |  |  |  |  |  |  | 9. Стоимость, всего, |  |  | руб. | Объектная смета | 4877632.98 | Прочие, руб. | 223279.76 | 9.08
Доработка грунта под отмостку и крыльца в ручную |  | 0.30 |  |  |  |  |  |  | в т.ч. СМР |  |  |  | Объектная смета | 3402575.05 | Итого сметная стоимость, руб. | 2458429.87 | 100.00
Устройство подсыпки из песка |  | 60.40 |  |  |  |  |  |  | 10. Стоимость на 1 м³ строительного объема |  |  | руб./м³ | 4877632,98 / 199180,8 | 24.49 | 7.3 |  | 100.00
Уплотнение грунта щебнем |  | 30.20 |  |  |  |  |  |  | 11. Стоимость СМР на 1 м³ строительного объема |  |  | руб./м³ | 3402575,05/199180,8 | 17.08 |  | Проектируемое здание
Устройство асфальтового покрытия отмостки и |  | 0.60 |  |  |  |  |  |  | 12. Стоимость на 1 м² общей площади |  |  | руб. / м² | 4877632,98/14976 | 325.70 | Наименование показателей | руб. | В процентах к итогу
 |  |  |  |  |  |  |  |  | 13. Стоимость СМР на 1 м² общей площади |  |  | руб. / м² | 3402575,05/14976 | 227.20 | Заработная плата рабочих, руб. | 851185 | 25.37
 | Общестроительные работы | 394835.68 | 92697.85 | 1400730.53 | 242190.74 | - |  | 1979831.30 | 14. Стоимость по сводному сметному расчету стоимости строительства, всего |  |  | руб. |  | 12006276.00 | Затраты на эксплуатацию строительных машин и механизмов, руб. | 238518 | 7.11
 |  |  | 37946.72 | 96893.37 | 272470.98 |  |  | 54764.51 |  |  |  |  | ССР |  | В том числе заработная плата рабочих, руб. |  | 0.00
 | Санитарно-технические работы (10%) | 39483.57 | 9269.79 | 140073.05 | 30649.65 | - |  | 258075.26 | В т.ч. | СМР |  | руб. | 12006276-4061724-2571165 | 5373387.00 | Материалы, руб. | 901089.00 | 26.85
 |  |  | 3794.67 | 9689.34 | 28909.86 |  |  | 8762.32 |  | Оборудование |  | руб. |  | 2571165.00 | Транспортные затраты, руб. | 69738.76 | 2.08
 | Слаботочные устройства, контрольно-измерительные приборы и автоматика (2%) | 7896.71 | 1853.96 | 28014.61 | 4509.59 | - |  | 47402.35 | 15. Стоимость по сводному сметному расчету на 1 м³ строительного объема |  |  | руб./м³ | 12006276/199180,8 | 60.28 | Общехозяйственные и общепроизводственные расходы, руб. | 524819 | 15.64
 |  |  | 758.93 | 1937.87 | 3189.61 |  |  | 2738.23 | 16. Стоимость СМР по сводному сметному расчету на 1 м³ строительного объема |  |  | руб./м³ | 5373387/199180,8 | 26.98 | Итого себестоимости СМР, руб. | 2585349.76 | 77.05
 | Электромонтажные работы (8%) | 31586.85 | 7415.83 | 112058.44 | 18038.37 | - |  | 189609.39 | 17. Стоимость по сводному сметному расчету на 1 м² общей площади |  |  | руб. / м² | 12006276/14976 | 801.70 | Плановая прибыль, руб. | 546826.00 | 16.30
 |  |  | 3035.74 | 7751.47 | 12758.43 |  |  | 8953.53 | 18. Стоимость СМР по сводному сметному расчету на 1 м² общей площади |  |  | руб. / м² | 3320260/14976 | 358.80 | Итого сметная стоимость, руб. | 3132175.76 | 93.35
 | Монтаж технологического оборудования | 47515.95 | 59394.94 | 83152.91 | 24149.18 | 1187898.78 | - | 1432221.23 | 19. Трудоемкость по сводному сметному расчету стоимости строительства |  |  | чел.-ч. | Объектная смета | 513560.00 | Прочие затраты | 223280.00 | 6.65
 |  |  | 24313.87 | 5751.97 | 24357.49 |  |  | 10952.90 | 20. Трудоемкость по объектной смете, всего |  |  | чел.-ч. |  | 211527.01 | Итого сметная стоимость СМР, руб. | 3355455.76 | 100.00
 | Итого | 521318.77 | 170632.36 | 1764029.55 | 319537.54 | 1187898.78 |  | 3907139.53 | 21 .Выработка на 1 чел.-дн., по объектной смете, всего |  |  | руб/чел-день | 4877632,98 /(211527,01/8) | 147.77
 |  |  | 69849.93 | 122024.02 | 341686.37 |  | 0.00 | 86171.49 | в т.ч СМР |  |  | руб/чел-день | 3402575,05/(211527,01/8) | 102.84
 |  |  |  |  |  |  | 4427127.38 | 2719240.75 | 22. Выработка на 1 чел.-дн. по сводному сметному расчету стоимости строительства, всего |  |  | руб/чел-день | 12006276/(513560/8) | 187.03
 |  |  |  |  |  |  |  | 3402575.05 | в т.ч. СМР |  |  | руб/чел-день | 5373387/(513560/8) | 83.70
 |  |  |  |  |  |  |  |  | 23. Материалоемкость |  |  | руб./руб. | 1648798/12006276 | 0.14
 |  |  |  |  |  |  |  |  | 24. Материалоотдача |  |  | руб./руб. | 12006276/1648798 | 7.28
 |  |  |  |  |  |  |  |  | 25. Нормативная продолжительность строительства |  |  | дней | ТКП | 262.00
 |  |  |  |  |  |  |  |  | 26. Фактическая продолжительность строительства |  |  | дней | Принимаем условно | 255.00
 |  |  |  |  |  |  |  |  | 27. Экономический эффект от сокращения продолжительности строительства |  |  | руб. | (0,5*563100,53*(262-255))/365 | 5032.51
 |  |  |  |  |  |  |  |  | 28. Общий экономический эффект |  |  | руб. | 5032,51+7703,14 | 12735.65
 |  |  |  |  |  |  |  |  | Наименование показателя | Расчетная | Значение показателя
 |  |  |  |  |  |  |  |  |  | формула,
 |  |  |  |  |  |  |  |  |  | обоснование показателя | Вариант 1 | Вариант 2
 |  |  |  |  |  |  |  |  | Заработная плата рабочих, р. | Локальная смета №2 | 3579.94 | 5350.98
 |  |  |  |  |  |  |  |  | Затраты на эксплуатацию строительных машин и механизмов, р. | Локальная смета №2 | 2208.81 | 3642.08
 |  |  |  |  |  |  |  |  | в том числе заработная плата рабочих, р.
 |  |  |  |  |  |  |  |  | Материалы, р. | Локальная смета №2 | 4067.03 | 5740.10
 |  |  |  |  |  |  |  |  | Транспортные затраты, р. | Локальная смета №2 | 128.00 | 180.65
 |  |  |  |  |  |  |  |  | Общехозяйственные и общепроизводственные расходы, р. | (Зп+Зп.маш)*57,48/100 | 2527.98 | 3845.10
 |  |  |  |  |  |  |  |  | Итого себестоимость СМР, р. |  | 12511.76 | 18758.91
 |  |  |  |  |  |  |  |  | Плановая прибыль | (Зп+Зп.маш)*63,54/100 | 2794.49 | 4250.48
 |  |  |  |  |  |  |  |  | Итого сметная стоимость СМР |  | 15306.25 | 23009.39 | 7703.14
 |  |  |  |  |  |  |  |  | Трудоемкость, чел.-час. | Локальная смета №2 | 92.36 | 139.90
 |  |  |  |  |  |  |  |  | Выработка на 1 человеко-день, р. |  | 1325.79 | 1315.76
 |  |  |  |  |  |  |  |  | Материалоотдача, р./р. |  | 3.76 | 4.01
 |  |  |  |  |  |  |  |  | Материалоемкость, р./р. |  | 0.27 | 0.25
 |  |  |  |  |  |  |  |  | Капитальные вложения в производственную базу, р. |  | 120.40 | 120.40
 |  |  |  |  |  |  |  |  | Фондоотдача, р./р. |  | 127.13 | 191.11
 |  |  |  |  |  |  |  |  | Фондоемкость, р./р. |  | 0.01 | 0.01
 |  |  |  |  |  |  |  |  | Сметный уровень рентабельности, % |  | 18.26 | 18.47
