AliakseiHryhoryeu/graduate-work-construction-engineer/2. Расчетно-конструктивный раздел/Пример/2/List_4.pdf

# Карта перемещений Теоретическое армирование нижней

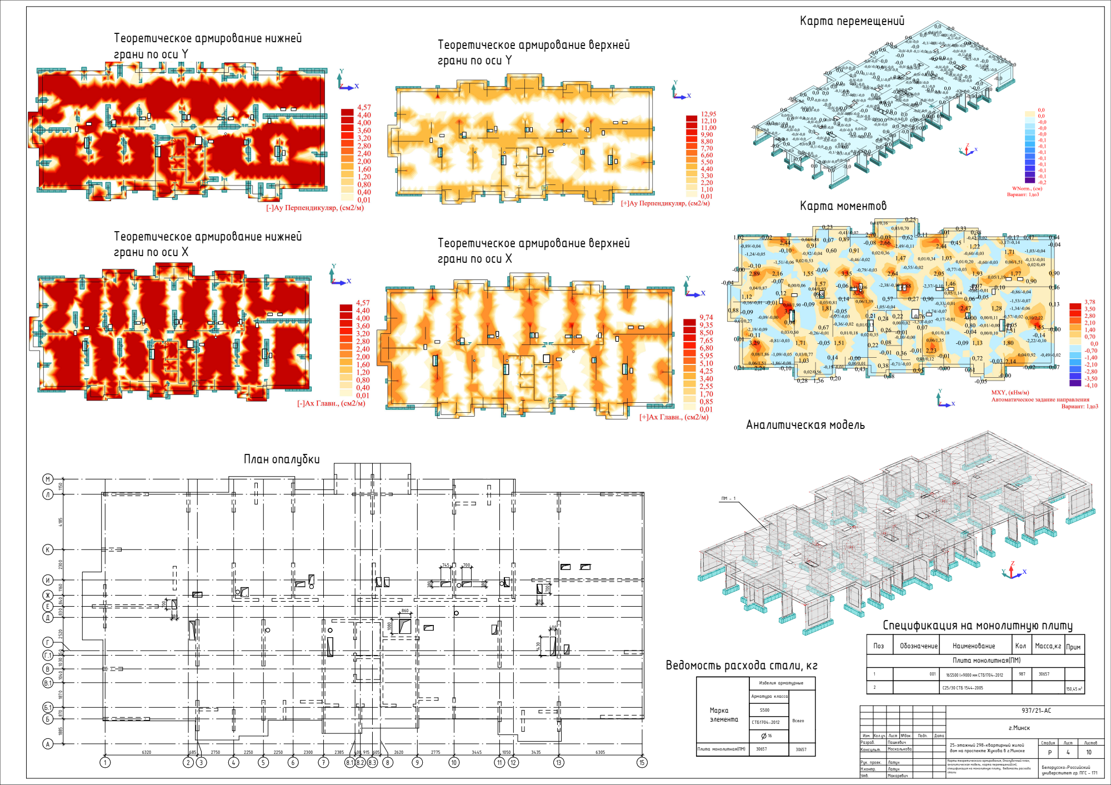
[picture p109: page 1]
План опалубки; Поз; Обозначение; Наименование; Кол; Масса,кг; Прим; СТБ1704-2012; Плита монолитная(ПМ); 10 ³⁰⁶⁵⁷; Аналитическая модель; Карта моментов; грани по оси Y; Теоретическое армирование верхней грани по оси Y; грани по оси X; Теоретическое армирование верхней грани по оси X

Теоретическое армирование нижней

Спецификация на монолитную плиту

Плита монолитная(ПМ)

Ведомость расхода стали, кг

1 | 001 | 16S500 l=9000 мм СТБ1704-2012 | 987 | 30657

Марка элемента | Изделия арматурные

2 | | C25/30 СТБ 1544-2005 | | | 150,45 м³

Арматура класса | Всего

г.Минск

Изм. | Кол.уч. | Лист | №док. | Подп. | Дата
Разраб. | Пашкевич | | | 25-этажный 298-квартирный жилой дом на проспекте Жукова в г.Минске | Стадия | Лист | Листов
Консульт. | Москалькова | | | | Р | 4

Рук. проек. | Латун | Карты теоретического армирования, Опалубочный план, аналитическая модель, карта перемещений(см), спецификация на монолитную плиту, ведомость расхода стали | Белорусско-Российский универститет гр. ПГС - 171
Н.контр. | Латун
Утв. | Макаревич
